MistyWest/polarTracker/Electrical/PCB Output Files/Gerber/PNG export/WW02 Mini RevB Top Silkscreen.pdf

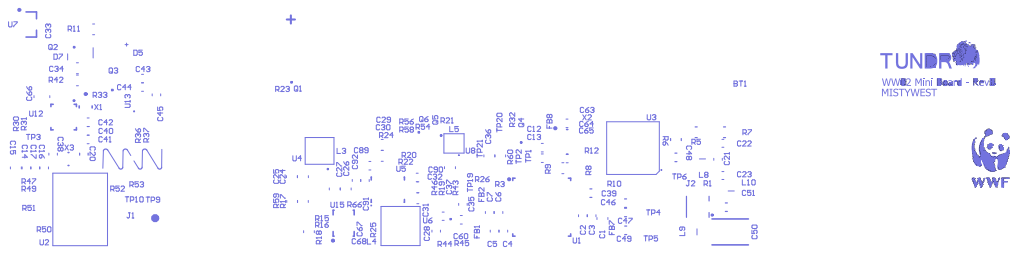
[picture p5: page 1]
