MistyWest/polarTracker/assets/WW02 Bear Tag_Arctic_backup.108.png

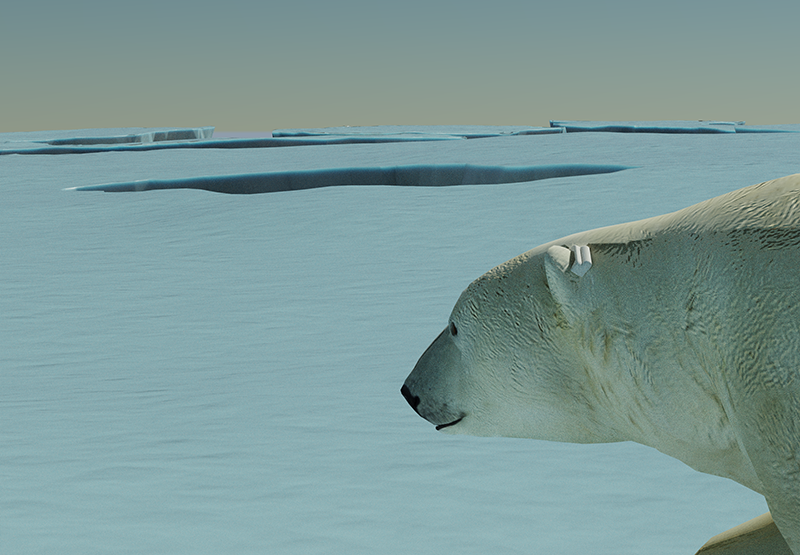
assets/WW02 Bear Tag_Arctic_backup.108.png
