MistyWest/polarTracker/Development Photos/Electrical Photos/image0.jpeg

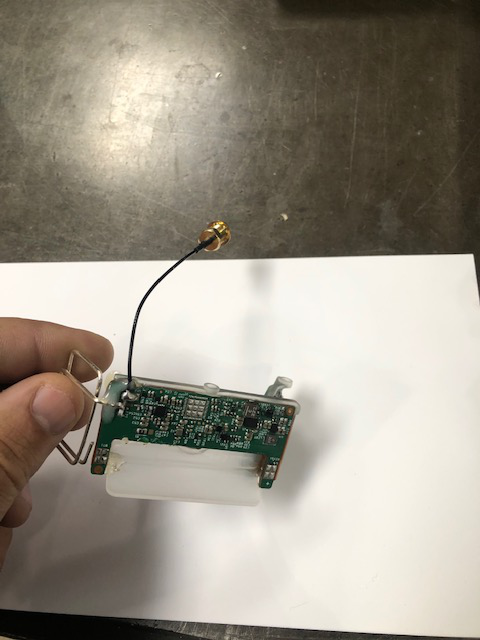
Development Photos/Electrical Photos/image0.jpeg
