MistyWest/polarTracker/Development Photos/Electrical Photos/image1.jpeg

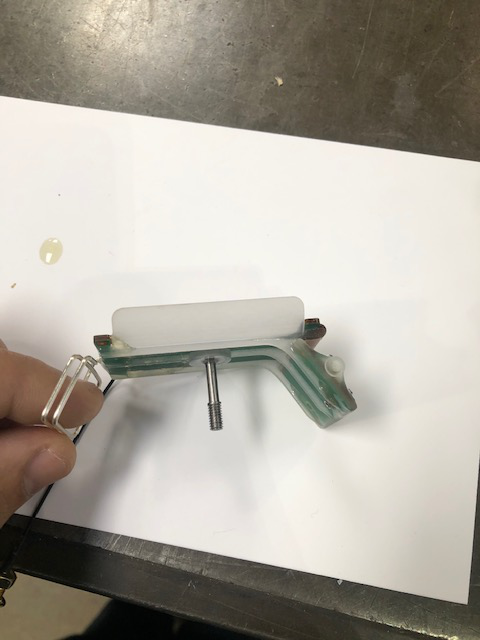
Development Photos/Electrical Photos/image1.jpeg
