MistyWest/polarTracker/Development Photos/Electrical Photos/image2.jpeg

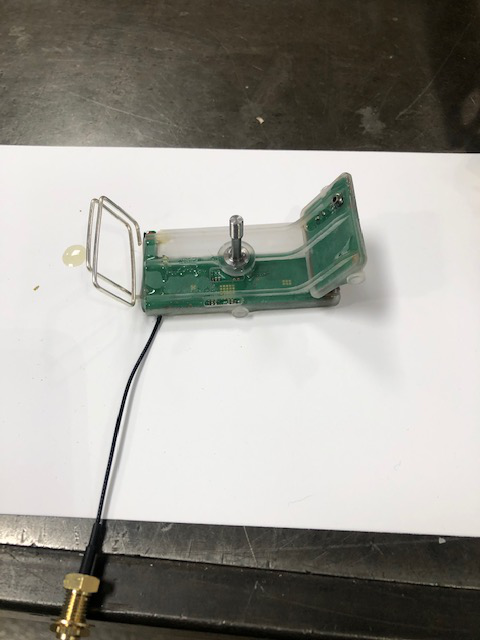
Development Photos/Electrical Photos/image2.jpeg
