MistyWest/polarTracker/Development Photos/Electrical Photos/PCB on Mount, U.FL Connector.jpg

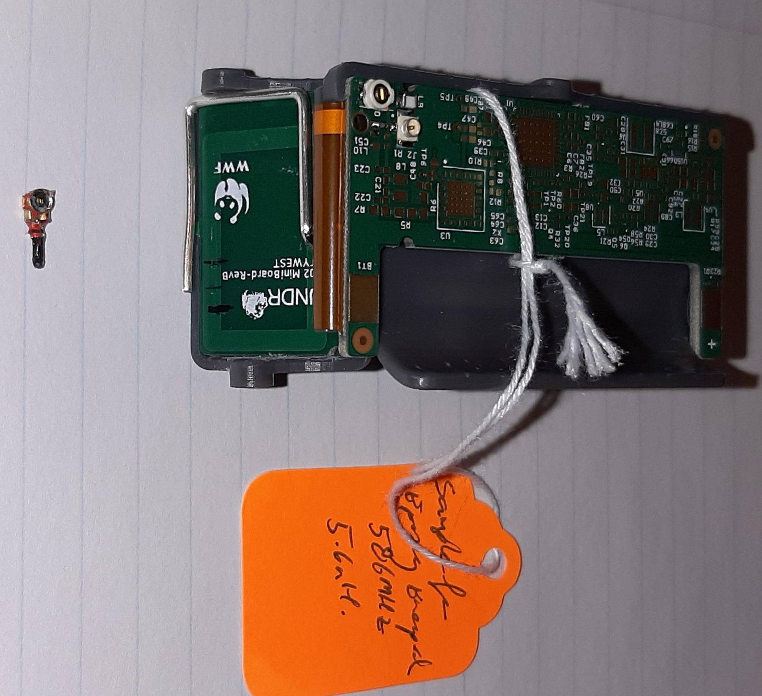
Development Photos/Electrical Photos/PCB on Mount, U.FL Connector.jpg
