MistyWest/polarTracker/Development Photos/Electrical Photos/PCB on Mount, UFL in place.jpg

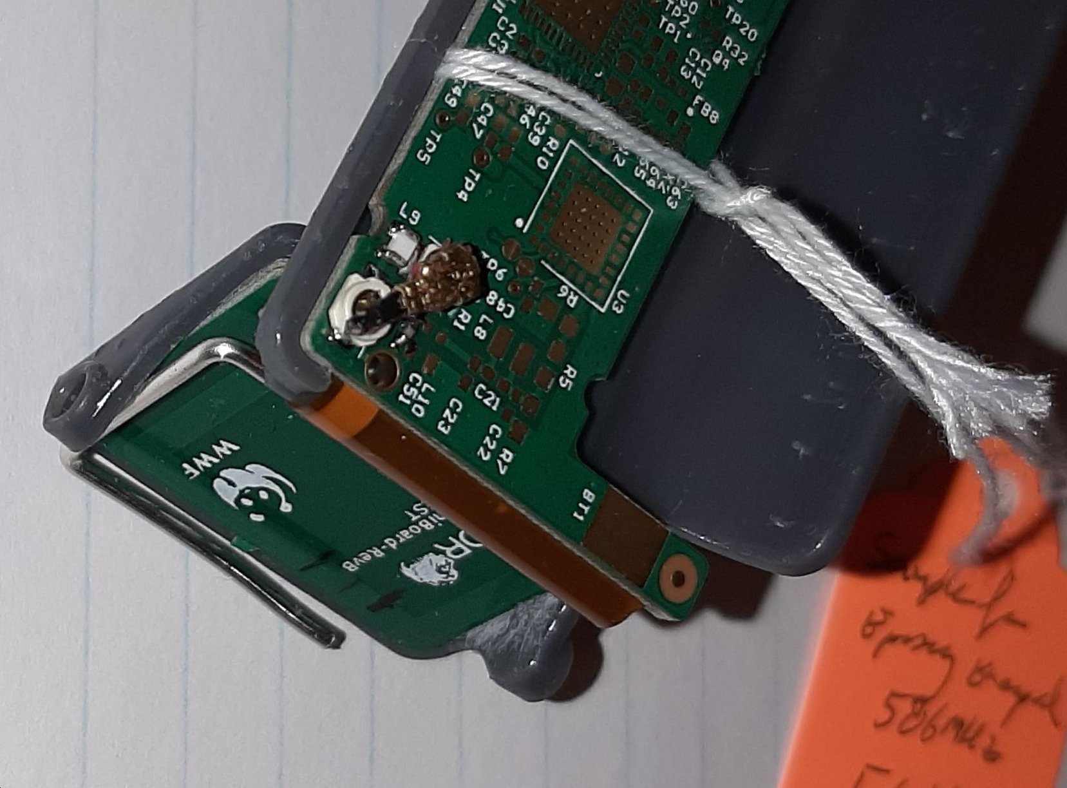
Development Photos/Electrical Photos/PCB on Mount, UFL in place.jpg
