MistyWest/polarTracker/Development Photos/Screenshot 2022-05-12 171735.png

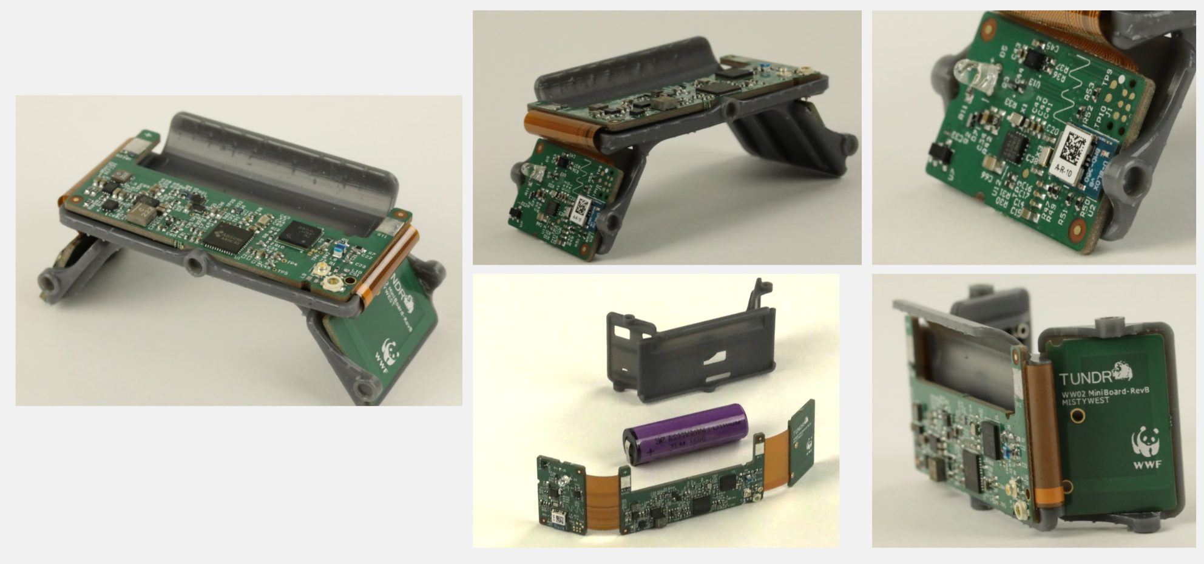
Development Photos/Screenshot 2022-05-12 171735.png
