MistyWest/polarTracker/Development Photos/Screenshot 2022-05-12 171948.png

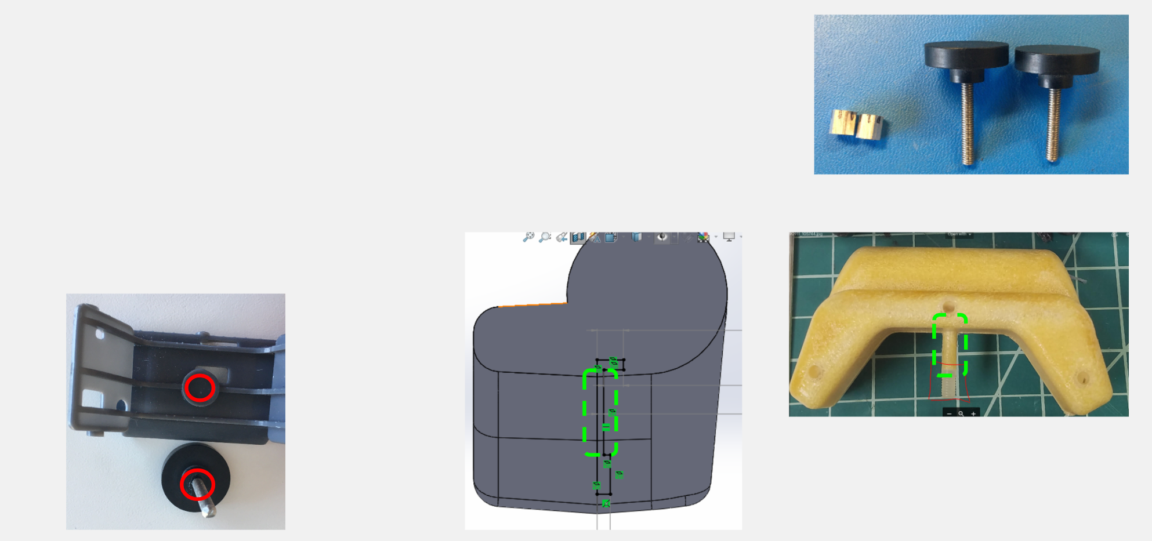
Development Photos/Screenshot 2022-05-12 171948.png
