MistyWest/polarTracker/Development Photos/Screenshot 2022-05-12 172118.png

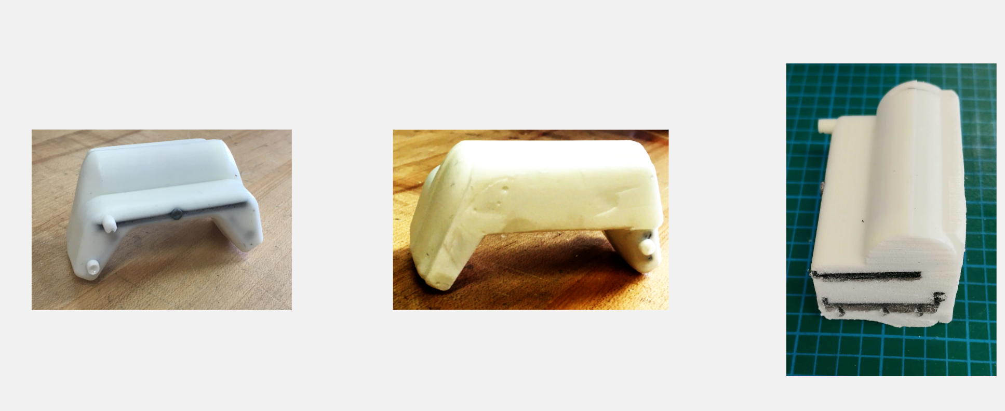
Development Photos/Screenshot 2022-05-12 172118.png
