MistyWest/polarTracker/Development Photos/Screenshot 2022-05-12 172450.png

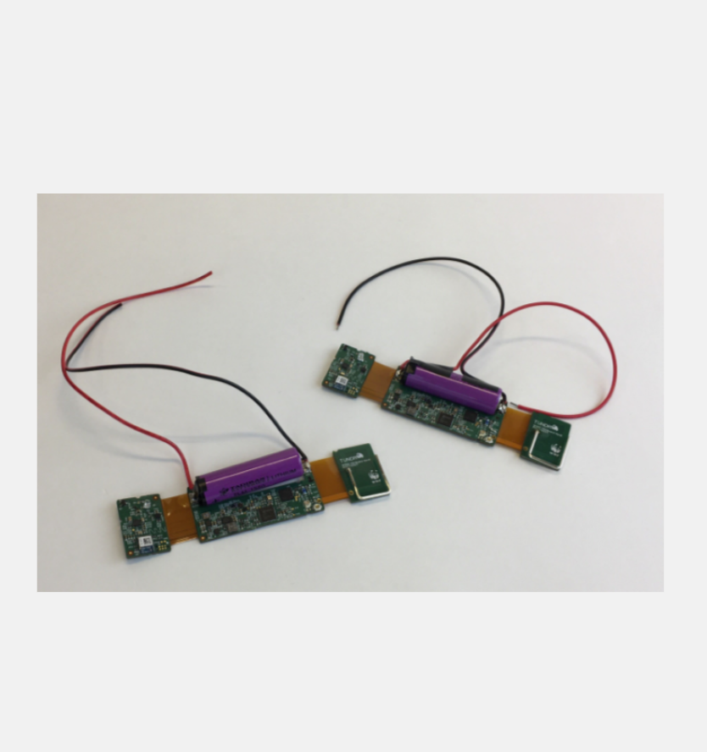
Development Photos/Screenshot 2022-05-12 172450.png
