MistyWest/polarTracker/Development Photos/Screenshot 2022-05-12 172559.png

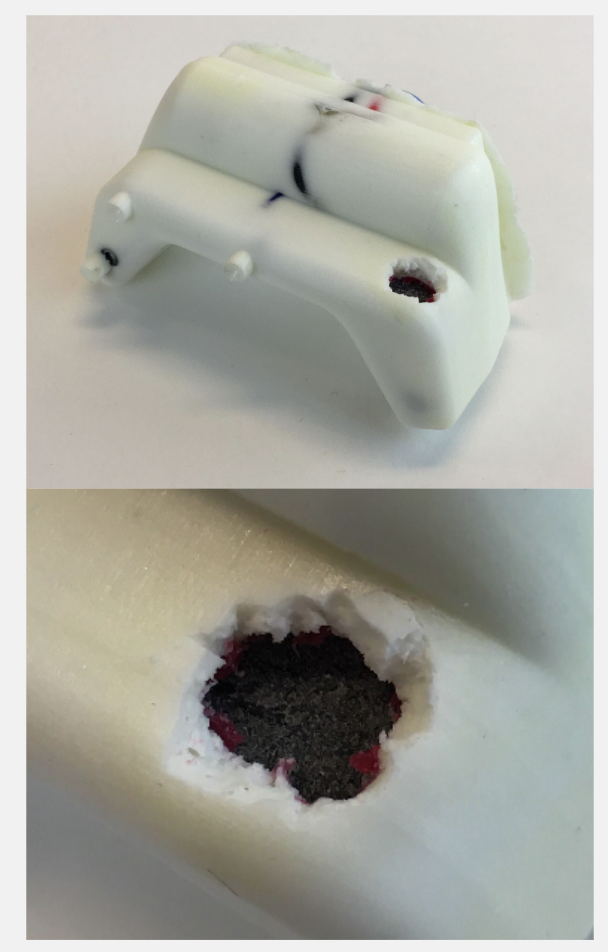
Development Photos/Screenshot 2022-05-12 172559.png
