MistyWest/polarTracker/Development Photos/Screenshot 2022-05-12 173209.png

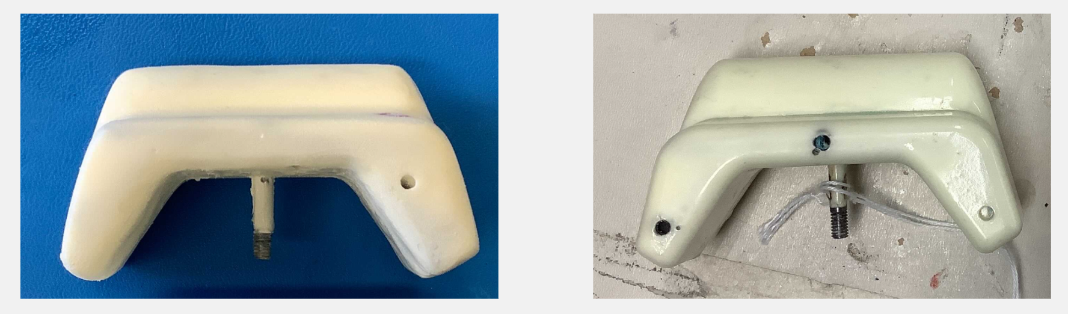
Development Photos/Screenshot 2022-05-12 173209.png
