MistyWest/polarTracker/Development Photos/Screenshot 2022-05-12 173252.png

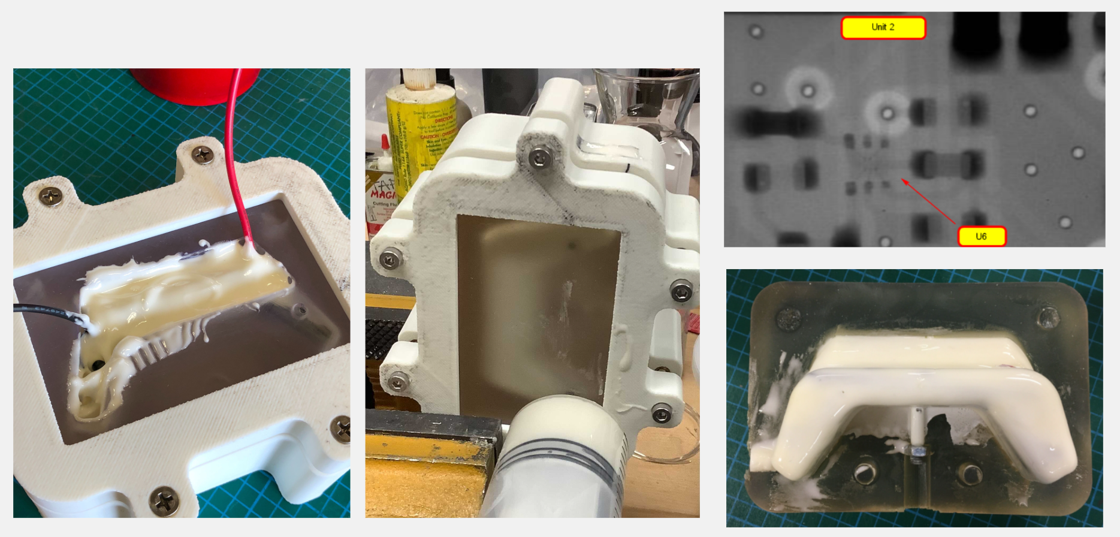
Development Photos/Screenshot 2022-05-12 173252.png
