MistyWest/polarTracker/Development Photos/WWF_340x460.png

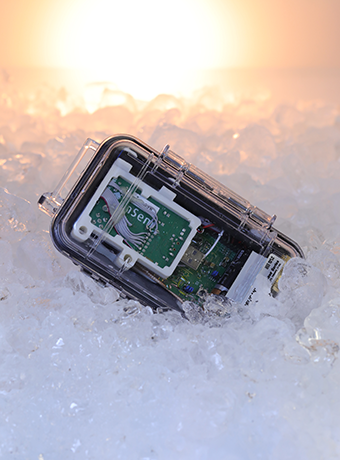
Development Photos/WWF_340x460.png
