MistyWest/polarTracker/Development Photos/WWF_Tracker03.png

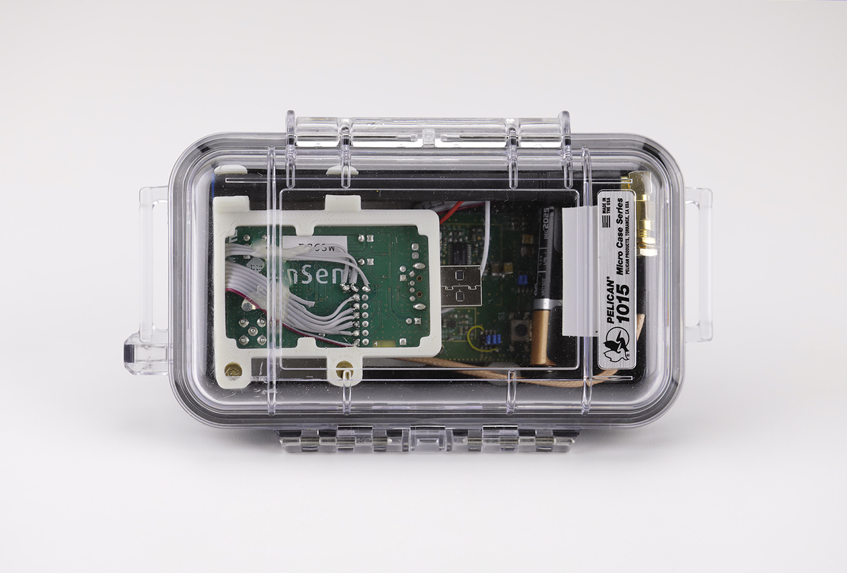
Development Photos/WWF_Tracker03.png
