MistyWest/polarTracker/Electrical/Images/WW02 Mini RevB Top Layer.png

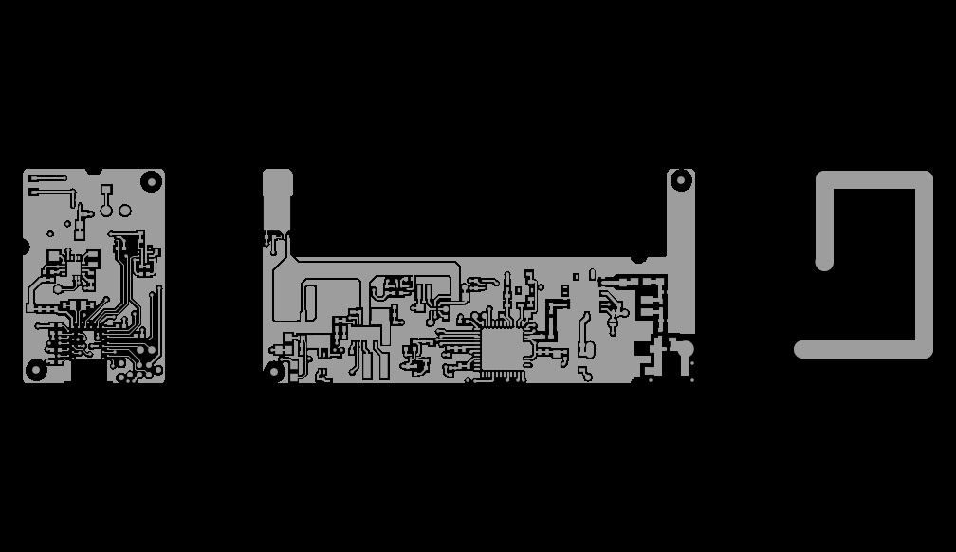
Electrical/Images/WW02 Mini RevB Top Layer.png
