MistyWest/polarTracker/Electrical/Images/WW02 Top Silkscreen.png

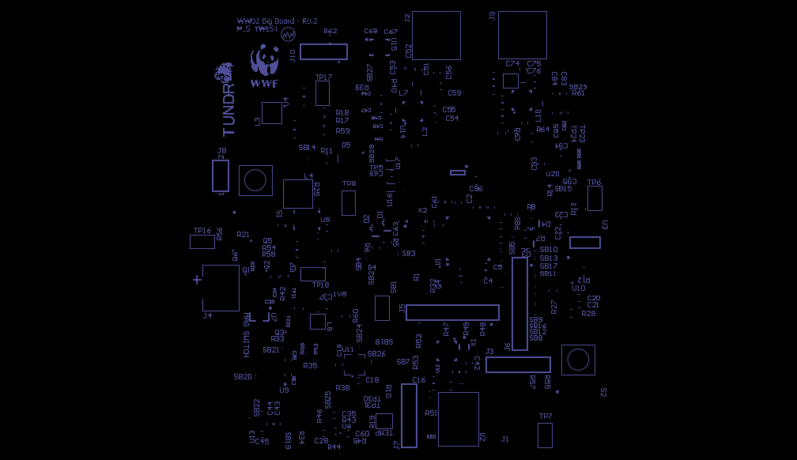
Electrical/Images/WW02 Top Silkscreen.png
