MistyWest/polarTracker/Electrical/Images/WW02_0000s_0003_Top-Layer-Right.png

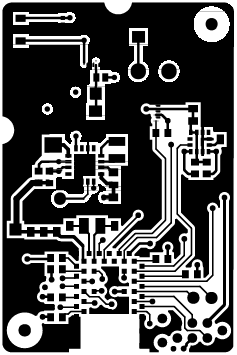
Electrical/Images/WW02_0000s_0003_Top-Layer-Right.png
