MistyWest/polarTracker/Electrical/Images/WW02_0002s_0002_Top-Layer-Middle.png

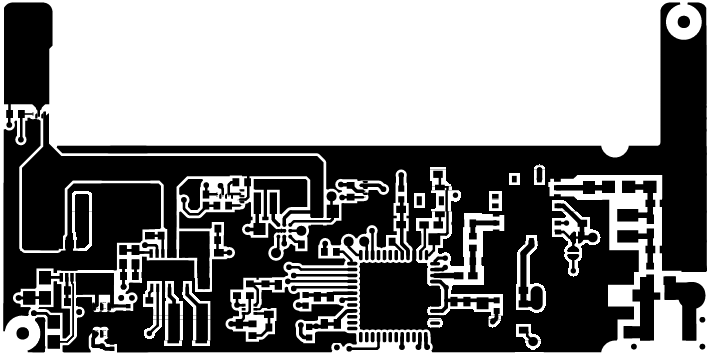
Electrical/Images/WW02_0002s_0002_Top-Layer-Middle.png
