MistyWest/polarTracker/Electrical/PCB Output Files/Gerber/PNG export/Photoshop png export/WW02_0001s_0002_Top-Layer-Antenna.png

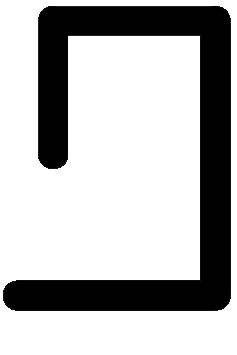
Electrical/PCB Output Files/Gerber/PNG export/Photoshop png export/WW02_0001s_0002_Top-Layer-Antenna.png
