MistyWest/polarTracker/Electrical/PCB Output Files/Gerber/PNG export/Photoshop png export/WW02_0002s_0000_Silkscreen-Middle.png

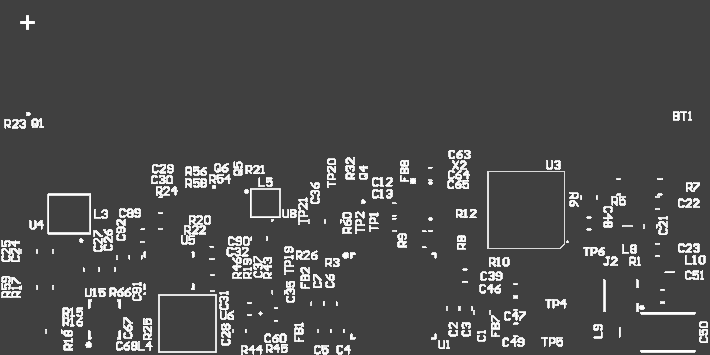
Electrical/PCB Output Files/Gerber/PNG export/Photoshop png export/WW02_0002s_0000_Silkscreen-Middle.png
