MistyWest/polarTracker/Electrical/PCB Output Files/Gerber/PNG export/Photoshop png export/WW02_0003s_0002_Top-Layer-copy-3.png

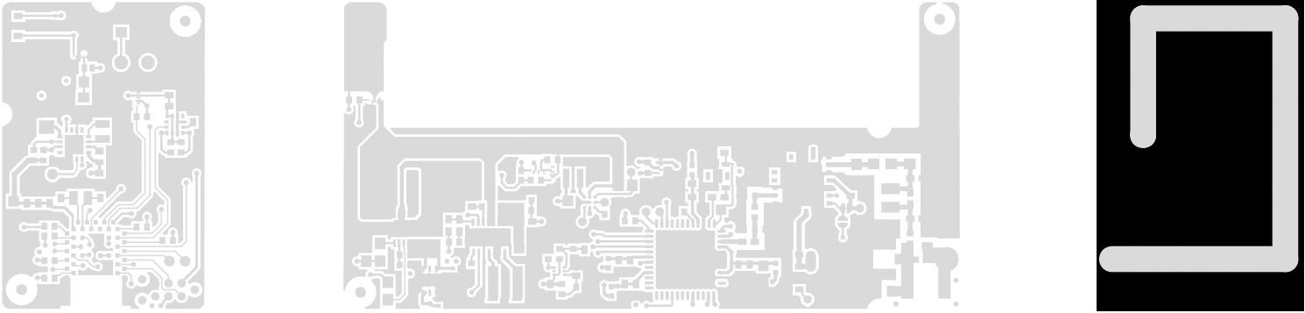
Electrical/PCB Output Files/Gerber/PNG export/Photoshop png export/WW02_0003s_0002_Top-Layer-copy-3.png
