MistyWest/polarTracker/Electrical/PCB Output Files/Gerber/PNG export/Photoshop png export/WW02_0003s_0003_Outline.png

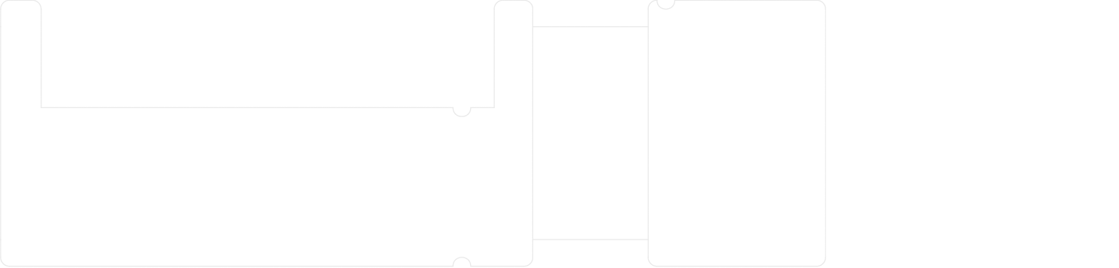
Electrical/PCB Output Files/Gerber/PNG export/Photoshop png export/WW02_0003s_0003_Outline.png
