MistyWest/polarTracker/Electrical/PCB Output Files/Gerber/PNG export/Silkscreen Antenna.png

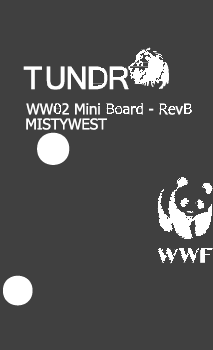
Electrical/PCB Output Files/Gerber/PNG export/Silkscreen Antenna.png
