MistyWest/polarTracker/Electrical/PCB Output Files/Gerber/PNG export/Silkscreen Right.png

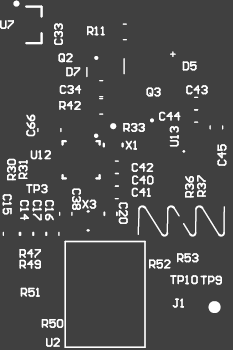
Electrical/PCB Output Files/Gerber/PNG export/Silkscreen Right.png
