MistyWest/polarTracker/Electrical/PCB Output Files/Gerber/PNG export/WW02 Mini RevB Board Outline.png

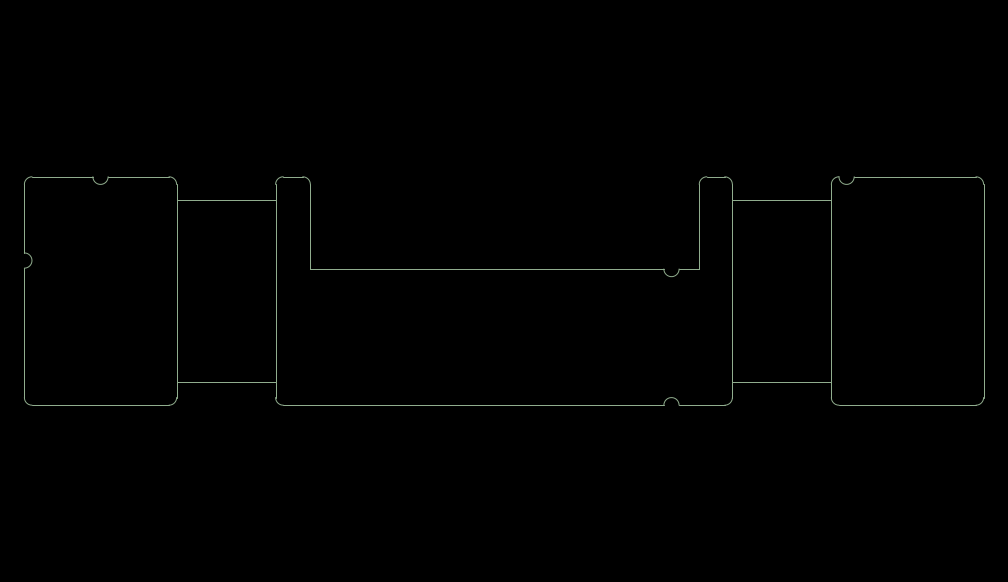
Electrical/PCB Output Files/Gerber/PNG export/WW02 Mini RevB Board Outline.png
