MistyWest/polarTracker/Electrical/PCB Output Files/Gerber/PNG export/WW02 Outline.png

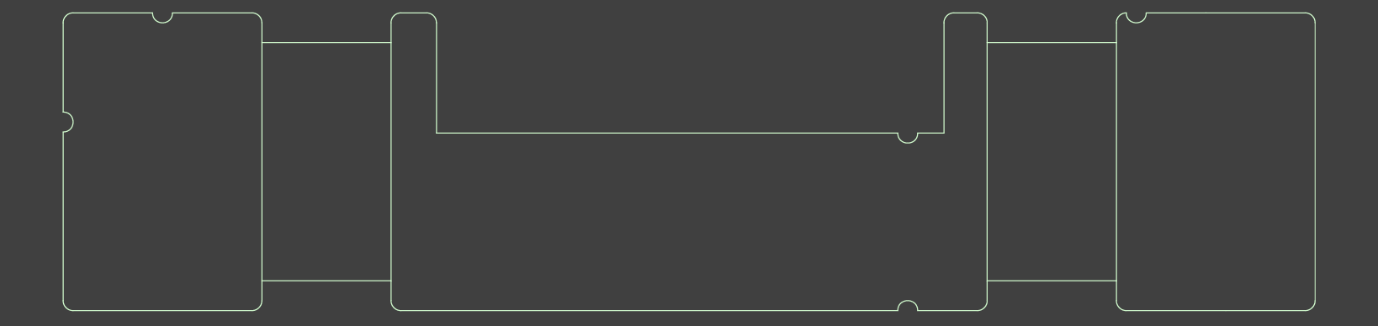
Electrical/PCB Output Files/Gerber/PNG export/WW02 Outline.png
