MistyWest/polarTracker/Electrical/PCB Output Files/Gerber/PNG export/WW02 Top Layer.png

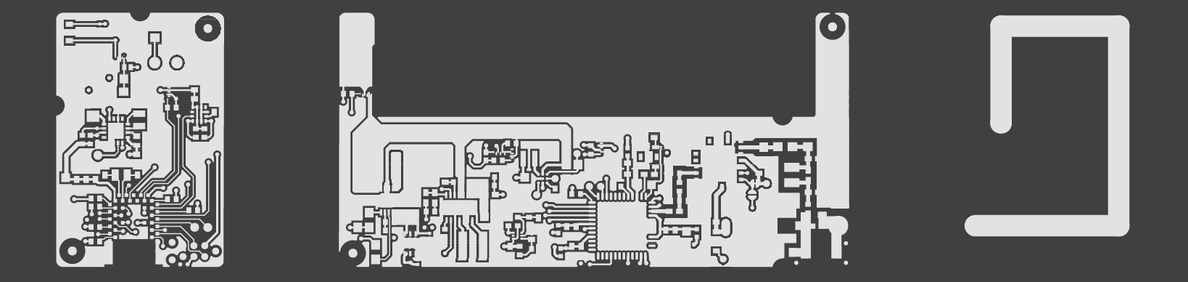
Electrical/PCB Output Files/Gerber/PNG export/WW02 Top Layer.png
