MistyWest/polarTracker/Electrical/PCB Output Files/Gerber/PNG export/WW02 Top Silkscreen.png

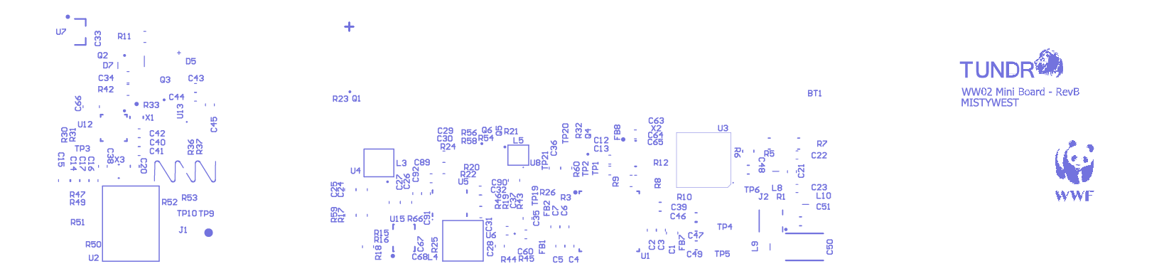
Electrical/PCB Output Files/Gerber/PNG export/WW02 Top Silkscreen.png
