MistyWest/polarTracker/Electrical/PCB Output Files/Gerber/PNG export/WW02_0000s_0001_Silkscreen-Right.png

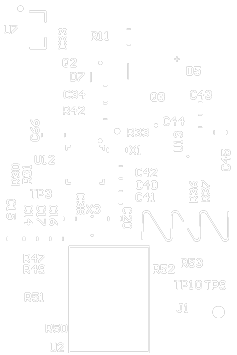
Electrical/PCB Output Files/Gerber/PNG export/WW02_0000s_0001_Silkscreen-Right.png
