MistyWest/polarTracker/Electrical/PCB Output Files/Gerber/PNG export/WW02_0001s_0000_Silkscreen-Antenna.png

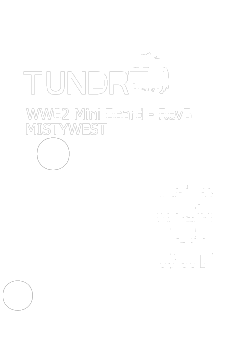
Electrical/PCB Output Files/Gerber/PNG export/WW02_0001s_0000_Silkscreen-Antenna.png
