MistyWest/polarTracker/Electrical/PCB Output Files/Stackup.jpg

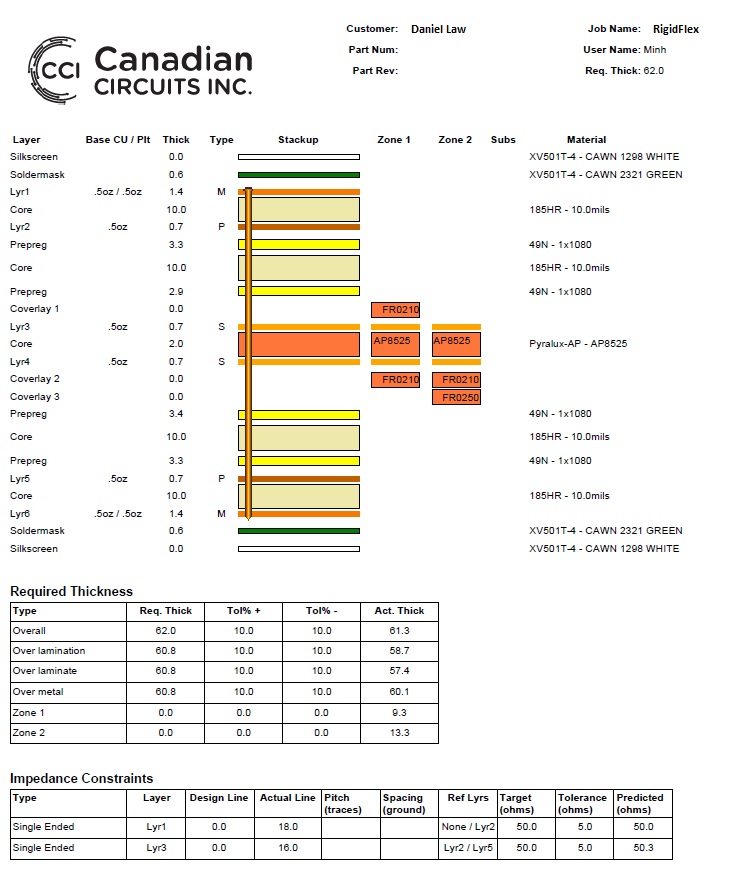
Electrical/PCB Output Files/Stackup.jpg
