MistyWest/polarTracker/Mechanical/3D Printed Mold v3/Hardware/90591A109_Zinc-Plated Steel Hex Nut.SLDPRT

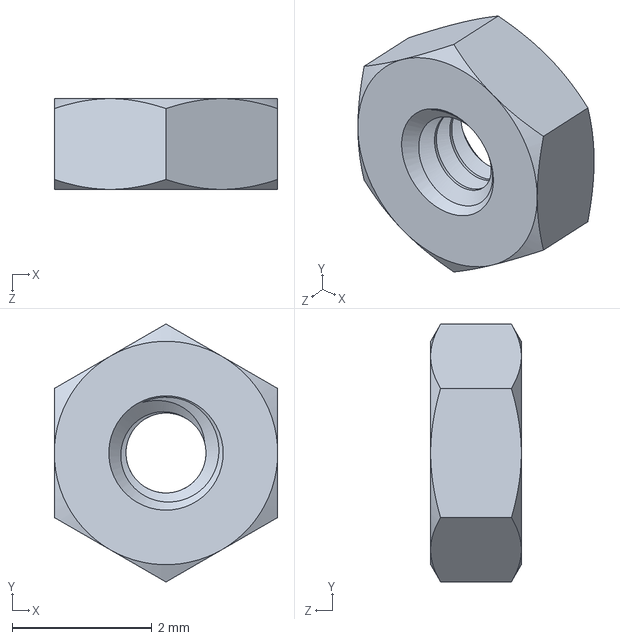
[picture p64: CAD file, 2022-04-27]
Mechanical/3D Printed Mold v3/Hardware/90591A109_Zinc-Plated Steel Hex Nut.SLDPRT
3.20 x 3.70 x 1.30 mm
