MistyWest/polarTracker/Mechanical/Mold v3/Hardware/90592A090_STEEL HEX NUT.SLDPRT

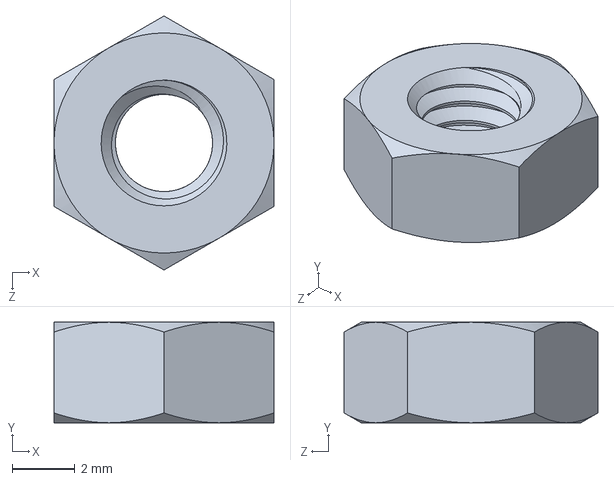
[picture p65: CAD file, 2022-04-28]
Mechanical/Mold v3/Hardware/90592A090_STEEL HEX NUT.SLDPRT
7.00 x 3.20 x 8.08 mm
