MistyWest/polarTracker/Mechanical/3D Printed Mold v3/Hardware/90358A009_Ultra-Low-Profile Socket Head Screw.SLDPRT

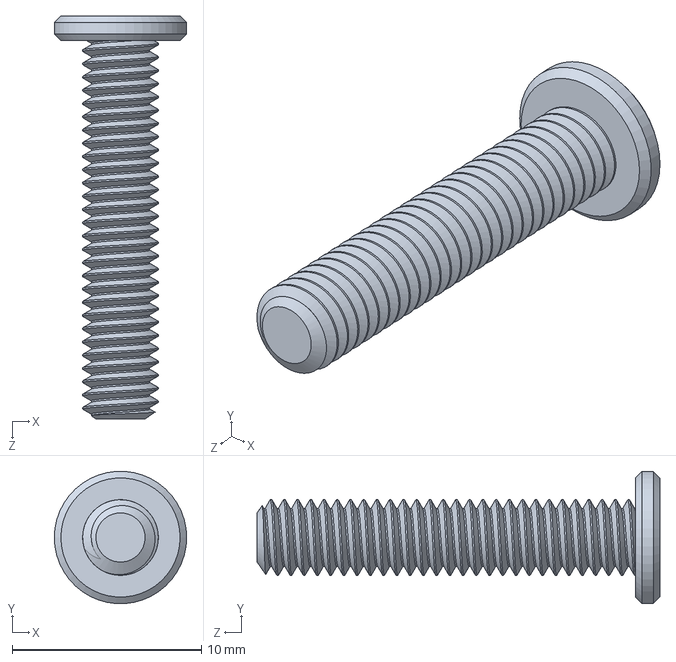
[picture p66: CAD file, 2022-04-27]
Mechanical/3D Printed Mold v3/Hardware/90358A009_Ultra-Low-Profile Socket Head Screw.SLDPRT
7.00 x 6.98 x 21.3 mm
