MistyWest/polarTracker/Mechanical/3D Printed Mold v3/Hardware/M4x0.7mmx20mm Ulow_prof.SLDPRT

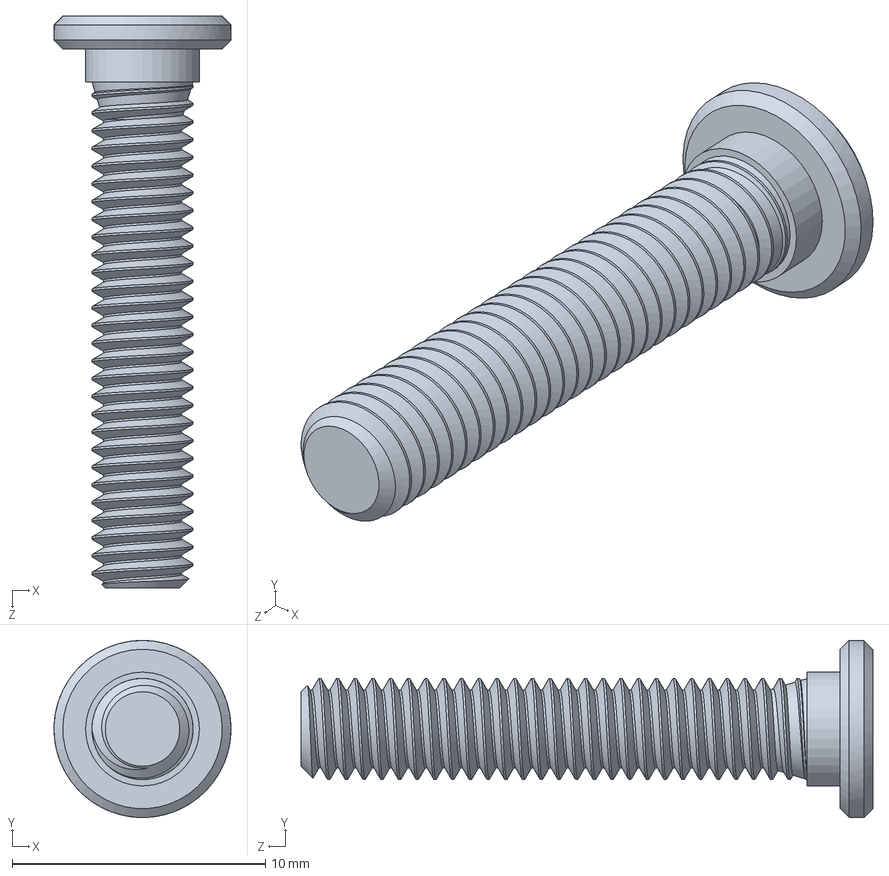
[picture p67: CAD file, 2022-04-27]
Mechanical/3D Printed Mold v3/Hardware/M4x0.7mmx20mm Ulow_prof.SLDPRT
7.00 x 7.00 x 22.6 mm
