MistyWest/polarTracker/Electrical/PCB Output Files/Gerber/PNG export/Photoshop png export/WW02_0000s_0002_Solder-Pads-Right.png

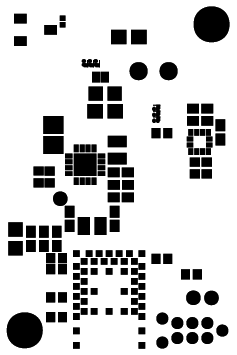
Electrical/PCB Output Files/Gerber/PNG export/Photoshop png export/WW02_0000s_0002_Solder-Pads-Right.png
