MistyWest/polarTracker/Electrical/PCB Output Files/Gerber/PNG export/Photoshop png export/WW02_0002s_0001_Solder-Pads-Middle.png

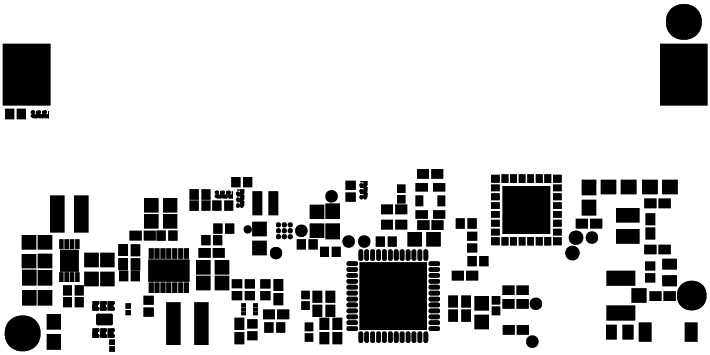
Electrical/PCB Output Files/Gerber/PNG export/Photoshop png export/WW02_0002s_0001_Solder-Pads-Middle.png
