MistyWest/polarTracker/Electrical/PCB Output Files/Gerber/PNG export/Solder Pads Right.png

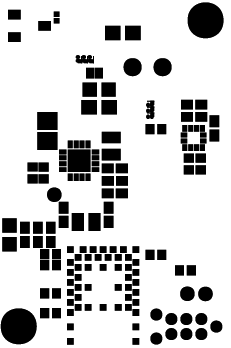
Electrical/PCB Output Files/Gerber/PNG export/Solder Pads Right.png
