MistyWest/polarTracker/Electrical/PCB Output Files/Gerber/PNG export/WW02 Mini RevB Solder Pads.png

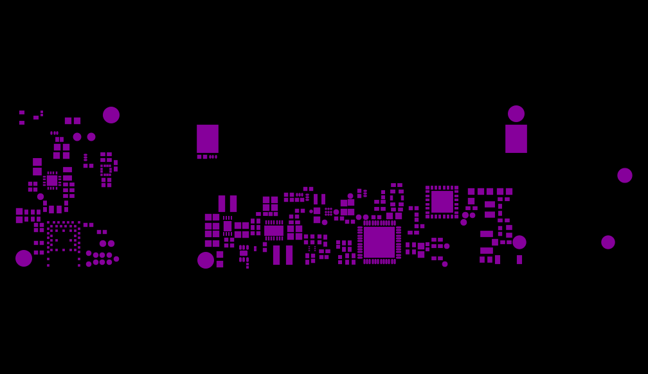
Electrical/PCB Output Files/Gerber/PNG export/WW02 Mini RevB Solder Pads.png
