MistyWest/polarTracker/Electrical/PCB Output Files/Gerber/PNG export/WW02 Solder.png

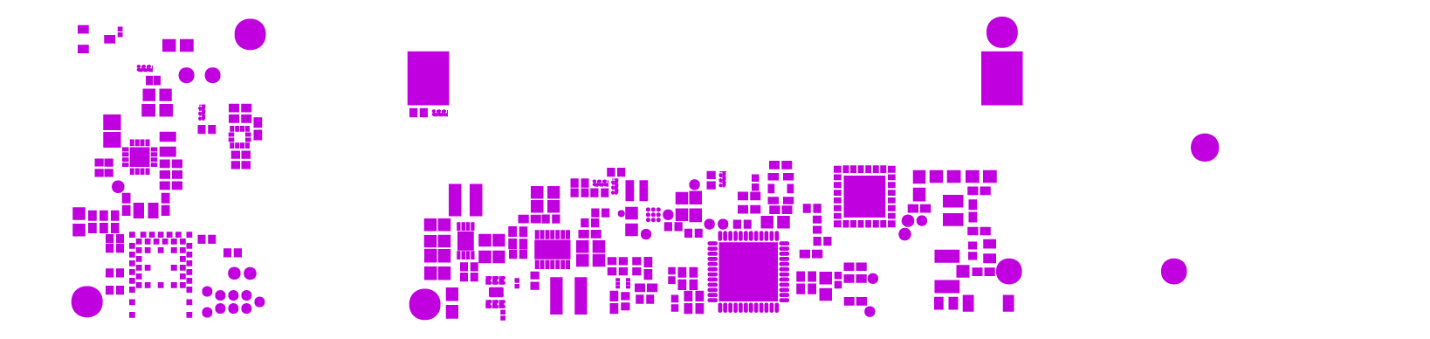
Electrical/PCB Output Files/Gerber/PNG export/WW02 Solder.png
