MistyWest/polarTracker/Testing and RF/Antenna versions, mounted tests.jpg

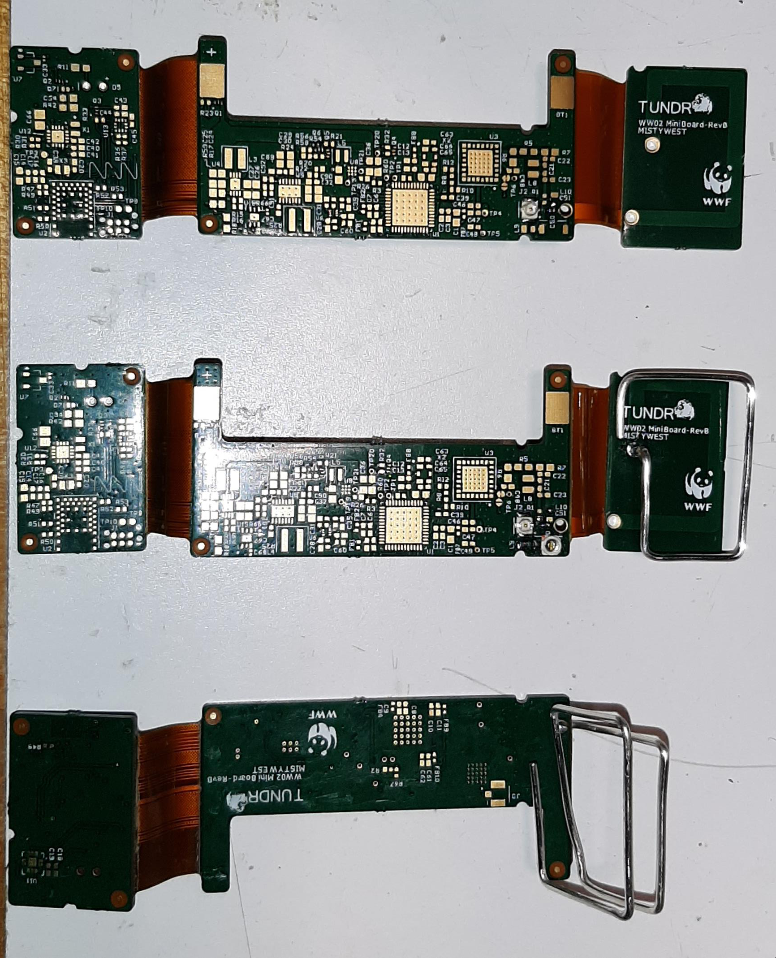
Testing and RF/Antenna versions, mounted tests.jpg
