MistyWest/polarTracker/Testing and RF/Hybrid Antenna on Test Unit.jpg

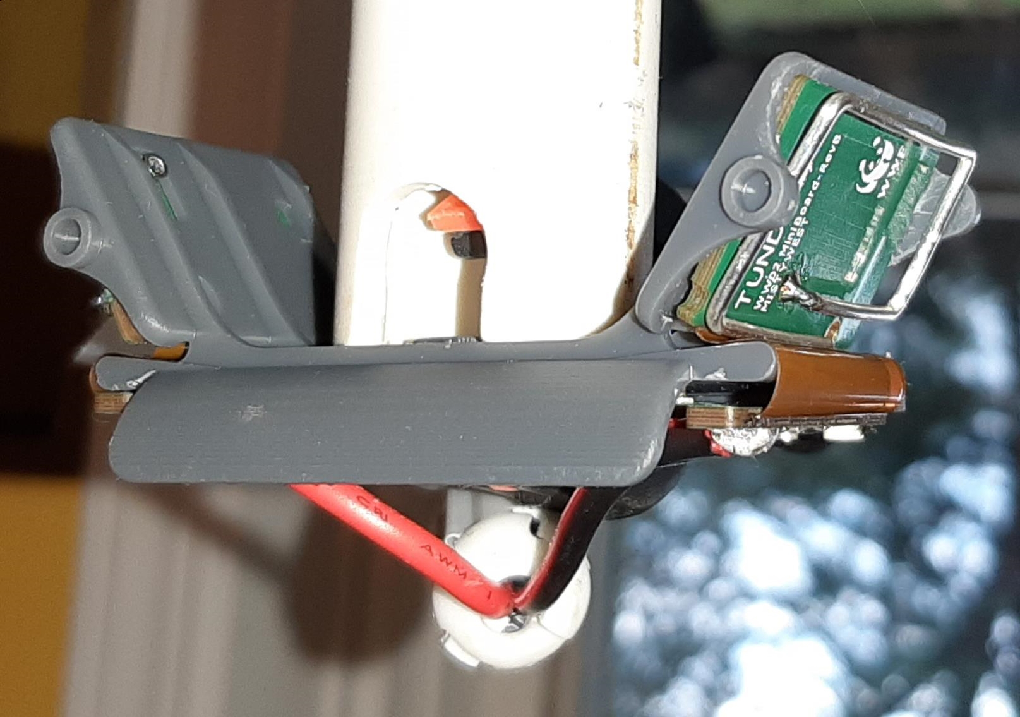
Testing and RF/Hybrid Antenna on Test Unit.jpg
