MistyWest/polarTracker/Testing and RF/IDEO_Feb_20.jpg

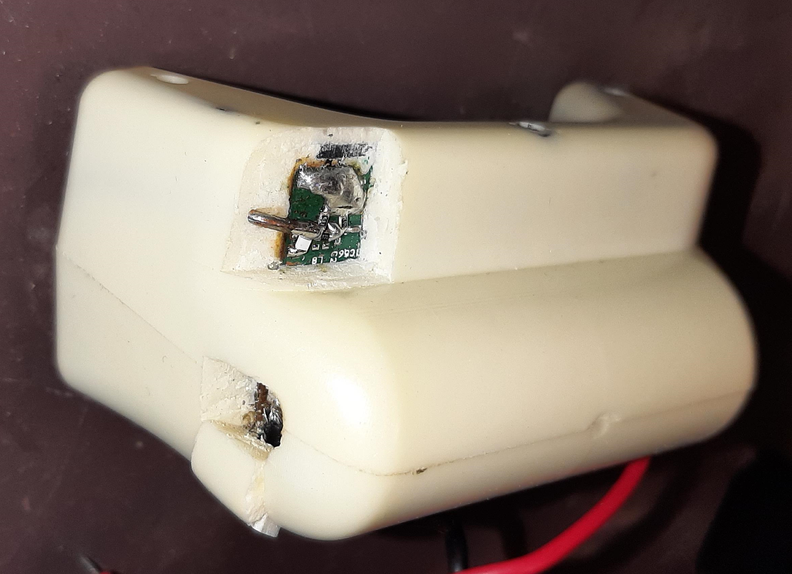
Testing and RF/IDEO_Feb_20.jpg
