MistyWest/polarTracker/Testing and RF/MW_Mar_21.jpg

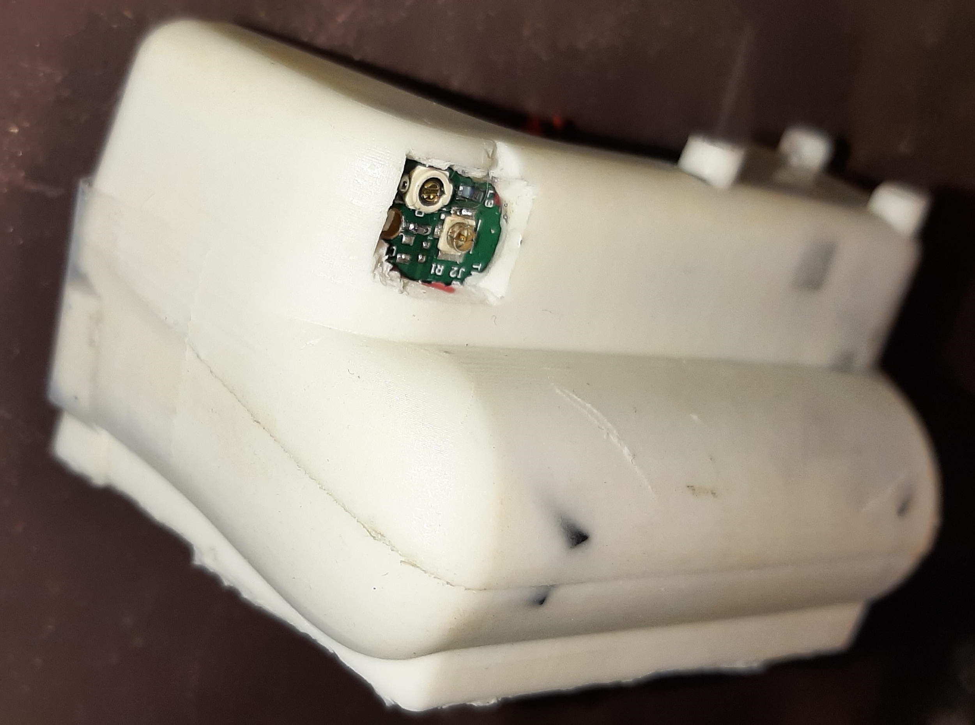
Testing and RF/MW_Mar_21.jpg
