MistyWest/polarTracker/Electrical/PCB Output Files/Gerber/PNG export/WW02 Mini RevB Top Layer.pdf

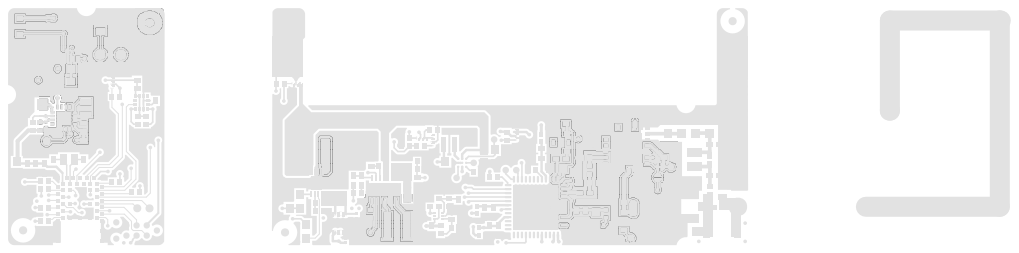
[picture p127: page 1]
