MistyWest/polarTracker/Firmware/ww02Firmware/CLI_Logging/mw_cli_settings.h

/*
 * mw_cli_settings.h
 *
 *  Created on: Jul 23, 2019
 *      Author: klockwood
 */

#ifndef CLI_LOGGING_MW_CLI_SETTINGS_H_
#define CLI_LOGGING_MW_CLI_SETTINGS_H_

#define CLI_TAG                                 "MistyWest>>"

#define cmdMAX_INPUT_SIZE                       100
#define cmdMAX_OUTPUT_SIZE                      100
#define cmdSOCKET_INPUT_BUFFER_SIZE             100

#define TIME_OUT                                20000

#define CLI_BUFFER_SIZE                         512
#define TX_BUF_SIZE                             2048
#define RX_BUF_SIZE                             256


#define CLI_THREAD_LOOP_DELAY                   200

#endif /* CLI_LOGGING_MW_CLI_SETTINGS_H_ */
