MistyWest/polarTracker/Firmware/ww02Firmware/SPI/mw_spi_device_settings.h

/*
 * spi_device_settings.h
 *
 *  Created on: Jan 21, 2019
 *      Author: klockwood
 */

/**@file
 *
 * @defgroup mw_spi_settings SPI Settings
 * @{
 * @ingroup  mw_spi
 * @brief    SPI settings.
 */

#ifndef SPI_MW_SPI_DEVICE_SETTINGS_H_
#define SPI_MW_SPI_DEVICE_SETTINGS_H_

#include "nrf_spi.h"
#include "nrf_spim.h"
#include "nrfx_spim.h"


#endif /* SPI_MW_SPI_DEVICE_SETTINGS_H_ */
