MistyWest/polarTracker/Firmware/ww02Firmware/mw_watchdog.h

/*
 * mw_watchdog.h
 *
 *  Created on: Oct 13, 2020
 *      Author: klockwood
 */

#ifndef UTIL_MW_WATCHDOG_H_
#define UTIL_MW_WATCHDOG_H_



void mw_watchdog_enable();

/**
 * @brief - Initializes WatchDog - Autostarts
 */
void mw_watchdog_init();

#endif /* UTIL_MW_WATCHDOG_H_ */
