MistyWest/polarTracker/Firmware/wwf_bootloader/_project_custom_board/config/sdk_config.h

/**
 * Copyright (c) 2017 - 2018, Nordic Semiconductor ASA
 *
 * All rights reserved.
 *
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
 * 3. Neither the name of Nordic Semiconductor ASA nor the names of its
 *    contributors may be used to endorse or promote products derived from this
 *    software without specific prior written permission.
 *
 * 4. This software, with or without modification, must only be used with a
 *    Nordic Semiconductor ASA integrated circuit.
 *
 * 5. Any software provided in binary form under this license must not be reverse
 *    engineered, decompiled, modified and/or disassembled.
 *
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
 */



#ifndef SDK_CONFIG_H
#define SDK_CONFIG_H
// <<< Use Configuration Wizard in Context Menu >>>\n

/* Use Project defined settings */
#include "mw_ble_dfu_settings.h"

#ifdef USE_APP_CONFIG
#include "app_config.h"
#endif
// <h> nRF_Bootloader

//==========================================================
// <h> nrf_bootloader - Bootloader settings

//==========================================================
// <h> Application integrity checks

//==========================================================
// <q> NRF_BL_APP_CRC_CHECK_SKIPPED_ON_GPREGRET2  - Skip integrity check of the application when bit 1 (0-indexed) is set in the GPREGRET2 register.


#ifndef NRF_BL_APP_CRC_CHECK_SKIPPED_ON_GPREGRET2
#define NRF_BL_APP_CRC_CHECK_SKIPPED_ON_GPREGRET2 1
#endif

// <q> NRF_BL_APP_CRC_CHECK_SKIPPED_ON_SYSTEMOFF_RESET  - Skip integrity check of the application when waking up from the System Off state.


#ifndef NRF_BL_APP_CRC_CHECK_SKIPPED_ON_SYSTEMOFF_RESET
#define NRF_BL_APP_CRC_CHECK_SKIPPED_ON_SYSTEMOFF_RESET 1
#endif

// </h>
//==========================================================

// <h> DFU mode enter method

//==========================================================
// <e> NRF_BL_DFU_ENTER_METHOD_BUTTON - Enter DFU mode on button press.
//==========================================================
#ifndef NRF_BL_DFU_ENTER_METHOD_BUTTON
#define NRF_BL_DFU_ENTER_METHOD_BUTTON 0
#endif
// <o> NRF_BL_DFU_ENTER_METHOD_BUTTON_PIN  - Button for entering DFU mode.

// <0=> 0 (P0.0)
// <1=> 1 (P0.1)
// <2=> 2 (P0.2)
// <3=> 3 (P0.3)
// <4=> 4 (P0.4)
// <5=> 5 (P0.5)
// <6=> 6 (P0.6)
// <7=> 7 (P0.7)
// <8=> 8 (P0.8)
// <9=> 9 (P0.9)
// <10=> 10 (P0.10)
// <11=> 11 (P0.11)
// <12=> 12 (P0.12)
// <13=> 13 (P0.13)
// <14=> 14 (P0.14)
// <15=> 15 (P0.15)
// <16=> 16 (P0.16)
// <17=> 17 (P0.17)
// <18=> 18 (P0.18)
// <19=> 19 (P0.19)
// <20=> 20 (P0.20)
// <21=> 21 (P0.21)
// <22=> 22 (P0.22)
// <23=> 23 (P0.23)
// <24=> 24 (P0.24)
// <25=> 25 (P0.25)
// <26=> 26 (P0.26)
// <27=> 27 (P0.27)
// <28=> 28 (P0.28)
// <29=> 29 (P0.29)
// <30=> 30 (P0.30)
// <31=> 31 (P0.31)

#ifndef NRF_BL_DFU_ENTER_METHOD_BUTTON_PIN
#define NRF_BL_DFU_ENTER_METHOD_BUTTON_PIN 16
#endif

// </e>

// <q> NRF_BL_DFU_ENTER_METHOD_PINRESET  - Enter DFU mode on pin reset.


#ifndef NRF_BL_DFU_ENTER_METHOD_PINRESET
#define NRF_BL_DFU_ENTER_METHOD_PINRESET 0
#endif

// <q> NRF_BL_DFU_ENTER_METHOD_GPREGRET  - Enter DFU mode when bit 1 (0-indexed) is set in the NRF_POWER_GPREGRET register.


#ifndef NRF_BL_DFU_ENTER_METHOD_GPREGRET
#define NRF_BL_DFU_ENTER_METHOD_GPREGRET 1
#endif

// <q> NRF_BL_DFU_ENTER_METHOD_BUTTONLESS  - Enter DFU mode when the Boolean enter_buttonless_dfu in DFU settings is true.


#ifndef NRF_BL_DFU_ENTER_METHOD_BUTTONLESS
#define NRF_BL_DFU_ENTER_METHOD_BUTTONLESS 0
#endif

// </h>
//==========================================================

// <h> DFU timers

//==========================================================
// <o> NRF_BL_DFU_CONTINUATION_TIMEOUT_MS - Timeout in ms when expecting an update immediately.  <100-60000000>


// <i> This timeout is used after updating the SoftDevice, when there is
// <i> already a valid application present. The bootloader will enter DFU mode
// <i> for a short time instead of booting the old application to allow the host
// <i> to immediately transfer a new application if it wishes.

#ifndef NRF_BL_DFU_CONTINUATION_TIMEOUT_MS
#define NRF_BL_DFU_CONTINUATION_TIMEOUT_MS 10000
#endif

// <o> NRF_BL_DFU_INACTIVITY_TIMEOUT_MS - Timeout in ms before automatically starting a valid application due to inactivity.  <0-60000000>


// <i> If 0, no inactivity timer will be used. Values 1-99 are invalid.

#ifndef NRF_BL_DFU_INACTIVITY_TIMEOUT_MS
#define NRF_BL_DFU_INACTIVITY_TIMEOUT_MS 120000
#endif

// </h>
//==========================================================

// <h> Watchdog timer

//==========================================================
// <o> NRF_BL_WDT_MAX_SCHEDULER_LATENCY_MS - Maximum latency of the scheduler in miliseconds
// <i> Maximum latency of the scheduler is compared with
// <i> watchdog counter reload value (CRV). If latency is big
// <i> enough, the watchdog will be fed from internal timer
// <i> handler along with feed from user function. If latency
// <i> is smaller than CRV, the watchdog will not be internally fed once
// <i> it will be externally fed. Maximum latency is mainly affected
// <i> by flash operations.

#ifndef NRF_BL_WDT_MAX_SCHEDULER_LATENCY_MS
#define NRF_BL_WDT_MAX_SCHEDULER_LATENCY_MS 10000
#endif

// </h>
//==========================================================

// <h> Misc Bootloader settings

//==========================================================
// <o> NRF_BL_FW_COPY_PROGRESS_STORE_STEP - Number of pages copied after which progress in the settings page is updated.
// <i> Progress stored in the settings page allows the bootloader to resume
// <i> copying the new firmware in case of interruption (reset).
// <i> If the value is small, then the resume point is more accurate. However,
// <i>  it also impacts negatively on flash wear.

#ifndef NRF_BL_FW_COPY_PROGRESS_STORE_STEP
#define NRF_BL_FW_COPY_PROGRESS_STORE_STEP 8
#endif

// </h>
//==========================================================

// </h>
//==========================================================

// </h>
//==========================================================

// <h> nRF_Crypto

//==========================================================
// <e> NRF_CRYPTO_ENABLED - nrf_crypto - Cryptography library.
//==========================================================
#ifndef NRF_CRYPTO_ENABLED
#define NRF_CRYPTO_ENABLED 1
#endif
// <o> NRF_CRYPTO_ALLOCATOR  - Memory allocator


// <i> Choose memory allocator used by nrf_crypto. Default is alloca if possible or nrf_malloc otherwise. If 'User macros' are selected, the user has to create 'nrf_crypto_allocator.h' file that contains NRF_CRYPTO_ALLOC, NRF_CRYPTO_FREE, and NRF_CRYPTO_ALLOC_ON_STACK.
// <0=> Default
// <1=> User macros
// <2=> On stack (alloca)
// <3=> C dynamic memory (malloc)
// <4=> SDK Memory Manager (nrf_malloc)

#ifndef NRF_CRYPTO_ALLOCATOR
#define NRF_CRYPTO_ALLOCATOR 0
#endif

// <e> NRF_CRYPTO_BACKEND_CC310_BL_ENABLED - Enable the ARM Cryptocell CC310 reduced backend.

// <i> The CC310 hardware-accelerated cryptography backend with reduced functionality and footprint (only available on nRF52840).
//==========================================================
#ifndef NRF_CRYPTO_BACKEND_CC310_BL_ENABLED
#define NRF_CRYPTO_BACKEND_CC310_BL_ENABLED 0
#endif
// <q> NRF_CRYPTO_BACKEND_CC310_BL_ECC_SECP224R1_ENABLED  - Enable the secp224r1 elliptic curve support using CC310_BL.


#ifndef NRF_CRYPTO_BACKEND_CC310_BL_ECC_SECP224R1_ENABLED
#define NRF_CRYPTO_BACKEND_CC310_BL_ECC_SECP224R1_ENABLED 0
#endif

// <q> NRF_CRYPTO_BACKEND_CC310_BL_ECC_SECP256R1_ENABLED  - Enable the secp256r1 elliptic curve support using CC310_BL.


#ifndef NRF_CRYPTO_BACKEND_CC310_BL_ECC_SECP256R1_ENABLED
#define NRF_CRYPTO_BACKEND_CC310_BL_ECC_SECP256R1_ENABLED 1
#endif

// <q> NRF_CRYPTO_BACKEND_CC310_BL_HASH_SHA256_ENABLED  - CC310_BL SHA-256 hash functionality.


// <i> CC310_BL backend implementation for hardware-accelerated SHA-256.

#ifndef NRF_CRYPTO_BACKEND_CC310_BL_HASH_SHA256_ENABLED
#define NRF_CRYPTO_BACKEND_CC310_BL_HASH_SHA256_ENABLED 1
#endif

// <q> NRF_CRYPTO_BACKEND_CC310_BL_HASH_AUTOMATIC_RAM_BUFFER_ENABLED  - nrf_cc310_bl buffers to RAM before running hash operation


// <i> Enabling this makes hashing of addresses in FLASH range possible. Size of buffer allocated for hashing is set by NRF_CRYPTO_BACKEND_CC310_BL_HASH_AUTOMATIC_RAM_BUFFER_SIZE

#ifndef NRF_CRYPTO_BACKEND_CC310_BL_HASH_AUTOMATIC_RAM_BUFFER_ENABLED
#define NRF_CRYPTO_BACKEND_CC310_BL_HASH_AUTOMATIC_RAM_BUFFER_ENABLED 0
#endif

// <o> NRF_CRYPTO_BACKEND_CC310_BL_HASH_AUTOMATIC_RAM_BUFFER_SIZE - nrf_cc310_bl hash outputs digests in little endian
// <i> Makes the nrf_cc310_bl hash functions output digests in little endian format. Only for use in nRF SDK DFU!

#ifndef NRF_CRYPTO_BACKEND_CC310_BL_HASH_AUTOMATIC_RAM_BUFFER_SIZE
#define NRF_CRYPTO_BACKEND_CC310_BL_HASH_AUTOMATIC_RAM_BUFFER_SIZE 4096
#endif

// </e>

// <e> NRF_CRYPTO_BACKEND_CC310_ENABLED - Enable the ARM Cryptocell CC310 backend.

// <i> The CC310 hardware-accelerated cryptography backend (only available on nRF52840).
//==========================================================
#ifndef NRF_CRYPTO_BACKEND_CC310_ENABLED
#define NRF_CRYPTO_BACKEND_CC310_ENABLED 0
#endif
// <q> NRF_CRYPTO_BACKEND_CC310_AES_CBC_ENABLED  - Enable the AES CBC mode using CC310.


#ifndef NRF_CRYPTO_BACKEND_CC310_AES_CBC_ENABLED
#define NRF_CRYPTO_BACKEND_CC310_AES_CBC_ENABLED 1
#endif

// <q> NRF_CRYPTO_BACKEND_CC310_AES_CTR_ENABLED  - Enable the AES CTR mode using CC310.


#ifndef NRF_CRYPTO_BACKEND_CC310_AES_CTR_ENABLED
#define NRF_CRYPTO_BACKEND_CC310_AES_CTR_ENABLED 1
#endif

// <q> NRF_CRYPTO_BACKEND_CC310_AES_ECB_ENABLED  - Enable the AES ECB mode using CC310.


#ifndef NRF_CRYPTO_BACKEND_CC310_AES_ECB_ENABLED
#define NRF_CRYPTO_BACKEND_CC310_AES_ECB_ENABLED 1
#endif

// <q> NRF_CRYPTO_BACKEND_CC310_AES_CBC_MAC_ENABLED  - Enable the AES CBC_MAC mode using CC310.


#ifndef NRF_CRYPTO_BACKEND_CC310_AES_CBC_MAC_ENABLED
#define NRF_CRYPTO_BACKEND_CC310_AES_CBC_MAC_ENABLED 1
#endif

// <q> NRF_CRYPTO_BACKEND_CC310_AES_CMAC_ENABLED  - Enable the AES CMAC mode using CC310.


#ifndef NRF_CRYPTO_BACKEND_CC310_AES_CMAC_ENABLED
#define NRF_CRYPTO_BACKEND_CC310_AES_CMAC_ENABLED 1
#endif

// <q> NRF_CRYPTO_BACKEND_CC310_AES_CCM_ENABLED  - Enable the AES CCM mode using CC310.


#ifndef NRF_CRYPTO_BACKEND_CC310_AES_CCM_ENABLED
#define NRF_CRYPTO_BACKEND_CC310_AES_CCM_ENABLED 1
#endif

// <q> NRF_CRYPTO_BACKEND_CC310_AES_CCM_STAR_ENABLED  - Enable the AES CCM* mode using CC310.


#ifndef NRF_CRYPTO_BACKEND_CC310_AES_CCM_STAR_ENABLED
#define NRF_CRYPTO_BACKEND_CC310_AES_CCM_STAR_ENABLED 1
#endif

// <q> NRF_CRYPTO_BACKEND_CC310_CHACHA_POLY_ENABLED  - Enable the CHACHA-POLY mode using CC310.


#ifndef NRF_CRYPTO_BACKEND_CC310_CHACHA_POLY_ENABLED
#define NRF_CRYPTO_BACKEND_CC310_CHACHA_POLY_ENABLED 1
#endif

// <q> NRF_CRYPTO_BACKEND_CC310_ECC_SECP160R1_ENABLED  - Enable the secp160r1 elliptic curve support using CC310.


#ifndef NRF_CRYPTO_BACKEND_CC310_ECC_SECP160R1_ENABLED
#define NRF_CRYPTO_BACKEND_CC310_ECC_SECP160R1_ENABLED 1
#endif

// <q> NRF_CRYPTO_BACKEND_CC310_ECC_SECP160R2_ENABLED  - Enable the secp160r2 elliptic curve support using CC310.


#ifndef NRF_CRYPTO_BACKEND_CC310_ECC_SECP160R2_ENABLED
#define NRF_CRYPTO_BACKEND_CC310_ECC_SECP160R2_ENABLED 1
#endif

// <q> NRF_CRYPTO_BACKEND_CC310_ECC_SECP192R1_ENABLED  - Enable the secp192r1 elliptic curve support using CC310.


#ifndef NRF_CRYPTO_BACKEND_CC310_ECC_SECP192R1_ENABLED
#define NRF_CRYPTO_BACKEND_CC310_ECC_SECP192R1_ENABLED 1
#endif

// <q> NRF_CRYPTO_BACKEND_CC310_ECC_SECP224R1_ENABLED  - Enable the secp224r1 elliptic curve support using CC310.


#ifndef NRF_CRYPTO_BACKEND_CC310_ECC_SECP224R1_ENABLED
#define NRF_CRYPTO_BACKEND_CC310_ECC_SECP224R1_ENABLED 1
#endif

// <q> NRF_CRYPTO_BACKEND_CC310_ECC_SECP256R1_ENABLED  - Enable the secp256r1 elliptic curve support using CC310.


#ifndef NRF_CRYPTO_BACKEND_CC310_ECC_SECP256R1_ENABLED
#define NRF_CRYPTO_BACKEND_CC310_ECC_SECP256R1_ENABLED 1
#endif

// <q> NRF_CRYPTO_BACKEND_CC310_ECC_SECP384R1_ENABLED  - Enable the secp384r1 elliptic curve support using CC310.


#ifndef NRF_CRYPTO_BACKEND_CC310_ECC_SECP384R1_ENABLED
#define NRF_CRYPTO_BACKEND_CC310_ECC_SECP384R1_ENABLED 1
#endif

// <q> NRF_CRYPTO_BACKEND_CC310_ECC_SECP521R1_ENABLED  - Enable the secp521r1 elliptic curve support using CC310.


#ifndef NRF_CRYPTO_BACKEND_CC310_ECC_SECP521R1_ENABLED
#define NRF_CRYPTO_BACKEND_CC310_ECC_SECP521R1_ENABLED 1
#endif

// <q> NRF_CRYPTO_BACKEND_CC310_ECC_SECP160K1_ENABLED  - Enable the secp160k1 elliptic curve support using CC310.


#ifndef NRF_CRYPTO_BACKEND_CC310_ECC_SECP160K1_ENABLED
#define NRF_CRYPTO_BACKEND_CC310_ECC_SECP160K1_ENABLED 1
#endif

// <q> NRF_CRYPTO_BACKEND_CC310_ECC_SECP192K1_ENABLED  - Enable the secp192k1 elliptic curve support using CC310.


#ifndef NRF_CRYPTO_BACKEND_CC310_ECC_SECP192K1_ENABLED
#define NRF_CRYPTO_BACKEND_CC310_ECC_SECP192K1_ENABLED 1
#endif

// <q> NRF_CRYPTO_BACKEND_CC310_ECC_SECP224K1_ENABLED  - Enable the secp224k1 elliptic curve support using CC310.


#ifndef NRF_CRYPTO_BACKEND_CC310_ECC_SECP224K1_ENABLED
#define NRF_CRYPTO_BACKEND_CC310_ECC_SECP224K1_ENABLED 1
#endif

// <q> NRF_CRYPTO_BACKEND_CC310_ECC_SECP256K1_ENABLED  - Enable the secp256k1 elliptic curve support using CC310.


#ifndef NRF_CRYPTO_BACKEND_CC310_ECC_SECP256K1_ENABLED
#define NRF_CRYPTO_BACKEND_CC310_ECC_SECP256K1_ENABLED 1
#endif

// <q> NRF_CRYPTO_BACKEND_CC310_ECC_CURVE25519_ENABLED  - Enable the Curve25519 curve support using CC310.


#ifndef NRF_CRYPTO_BACKEND_CC310_ECC_CURVE25519_ENABLED
#define NRF_CRYPTO_BACKEND_CC310_ECC_CURVE25519_ENABLED 1
#endif

// <q> NRF_CRYPTO_BACKEND_CC310_ECC_ED25519_ENABLED  - Enable the Ed25519 curve support using CC310.


#ifndef NRF_CRYPTO_BACKEND_CC310_ECC_ED25519_ENABLED
#define NRF_CRYPTO_BACKEND_CC310_ECC_ED25519_ENABLED 1
#endif

// <q> NRF_CRYPTO_BACKEND_CC310_HASH_SHA256_ENABLED  - CC310 SHA-256 hash functionality.


// <i> CC310 backend implementation for hardware-accelerated SHA-256.

#ifndef NRF_CRYPTO_BACKEND_CC310_HASH_SHA256_ENABLED
#define NRF_CRYPTO_BACKEND_CC310_HASH_SHA256_ENABLED 1
#endif

// <q> NRF_CRYPTO_BACKEND_CC310_HASH_SHA512_ENABLED  - CC310 SHA-512 hash functionality


// <i> CC310 backend implementation for SHA-512 (in software).

#ifndef NRF_CRYPTO_BACKEND_CC310_HASH_SHA512_ENABLED
#define NRF_CRYPTO_BACKEND_CC310_HASH_SHA512_ENABLED 1
#endif

// <q> NRF_CRYPTO_BACKEND_CC310_HMAC_SHA256_ENABLED  - CC310 HMAC using SHA-256


// <i> CC310 backend implementation for HMAC using hardware-accelerated SHA-256.

#ifndef NRF_CRYPTO_BACKEND_CC310_HMAC_SHA256_ENABLED
#define NRF_CRYPTO_BACKEND_CC310_HMAC_SHA256_ENABLED 1
#endif

// <q> NRF_CRYPTO_BACKEND_CC310_HMAC_SHA512_ENABLED  - CC310 HMAC using SHA-512


// <i> CC310 backend implementation for HMAC using SHA-512 (in software).

#ifndef NRF_CRYPTO_BACKEND_CC310_HMAC_SHA512_ENABLED
#define NRF_CRYPTO_BACKEND_CC310_HMAC_SHA512_ENABLED 1
#endif

// <q> NRF_CRYPTO_BACKEND_CC310_RNG_ENABLED  - Enable RNG support using CC310.


#ifndef NRF_CRYPTO_BACKEND_CC310_RNG_ENABLED
#define NRF_CRYPTO_BACKEND_CC310_RNG_ENABLED 1
#endif

// </e>

// <e> NRF_CRYPTO_BACKEND_CIFRA_ENABLED - Enable the Cifra backend.
//==========================================================
#ifndef NRF_CRYPTO_BACKEND_CIFRA_ENABLED
#define NRF_CRYPTO_BACKEND_CIFRA_ENABLED 0
#endif
// <q> NRF_CRYPTO_BACKEND_CIFRA_AES_EAX_ENABLED  - Enable the AES EAX mode using Cifra.


#ifndef NRF_CRYPTO_BACKEND_CIFRA_AES_EAX_ENABLED
#define NRF_CRYPTO_BACKEND_CIFRA_AES_EAX_ENABLED 1
#endif

// </e>

// <e> NRF_CRYPTO_BACKEND_MBEDTLS_ENABLED - Enable the mbed TLS backend.
//==========================================================
#ifndef NRF_CRYPTO_BACKEND_MBEDTLS_ENABLED
#define NRF_CRYPTO_BACKEND_MBEDTLS_ENABLED 0
#endif
// <q> NRF_CRYPTO_BACKEND_MBEDTLS_AES_CBC_ENABLED  - Enable the AES CBC mode mbed TLS.


#ifndef NRF_CRYPTO_BACKEND_MBEDTLS_AES_CBC_ENABLED
#define NRF_CRYPTO_BACKEND_MBEDTLS_AES_CBC_ENABLED 1
#endif

// <q> NRF_CRYPTO_BACKEND_MBEDTLS_AES_CTR_ENABLED  - Enable the AES CTR mode using mbed TLS.


#ifndef NRF_CRYPTO_BACKEND_MBEDTLS_AES_CTR_ENABLED
#define NRF_CRYPTO_BACKEND_MBEDTLS_AES_CTR_ENABLED 1
#endif

// <q> NRF_CRYPTO_BACKEND_MBEDTLS_AES_CFB_ENABLED  - Enable the AES CFB mode using mbed TLS.


#ifndef NRF_CRYPTO_BACKEND_MBEDTLS_AES_CFB_ENABLED
#define NRF_CRYPTO_BACKEND_MBEDTLS_AES_CFB_ENABLED 1
#endif

// <q> NRF_CRYPTO_BACKEND_MBEDTLS_AES_ECB_ENABLED  - Enable the AES ECB mode using mbed TLS.


#ifndef NRF_CRYPTO_BACKEND_MBEDTLS_AES_ECB_ENABLED
#define NRF_CRYPTO_BACKEND_MBEDTLS_AES_ECB_ENABLED 1
#endif

// <q> NRF_CRYPTO_BACKEND_MBEDTLS_AES_CBC_MAC_ENABLED  - Enable the AES CBC MAC mode using mbed TLS.


#ifndef NRF_CRYPTO_BACKEND_MBEDTLS_AES_CBC_MAC_ENABLED
#define NRF_CRYPTO_BACKEND_MBEDTLS_AES_CBC_MAC_ENABLED 1
#endif

// <q> NRF_CRYPTO_BACKEND_MBEDTLS_AES_CMAC_ENABLED  - Enable the AES CMAC mode using mbed TLS.


#ifndef NRF_CRYPTO_BACKEND_MBEDTLS_AES_CMAC_ENABLED
#define NRF_CRYPTO_BACKEND_MBEDTLS_AES_CMAC_ENABLED 1
#endif

// <q> NRF_CRYPTO_BACKEND_MBEDTLS_AES_CCM_ENABLED  - Enable the AES CCM mode using mbed TLS.


#ifndef NRF_CRYPTO_BACKEND_MBEDTLS_AES_CCM_ENABLED
#define NRF_CRYPTO_BACKEND_MBEDTLS_AES_CCM_ENABLED 1
#endif

// <q> NRF_CRYPTO_BACKEND_MBEDTLS_AES_GCM_ENABLED  - Enable the AES GCM mode using mbed TLS.


#ifndef NRF_CRYPTO_BACKEND_MBEDTLS_AES_GCM_ENABLED
#define NRF_CRYPTO_BACKEND_MBEDTLS_AES_GCM_ENABLED 1
#endif

// <q> NRF_CRYPTO_BACKEND_MBEDTLS_ECC_SECP192R1_ENABLED  - Enable secp192r1 (NIST 192-bit) curve


// <i> Enable this setting if you need secp192r1 (NIST 192-bit) support using MBEDTLS

#ifndef NRF_CRYPTO_BACKEND_MBEDTLS_ECC_SECP192R1_ENABLED
#define NRF_CRYPTO_BACKEND_MBEDTLS_ECC_SECP192R1_ENABLED 1
#endif

// <q> NRF_CRYPTO_BACKEND_MBEDTLS_ECC_SECP224R1_ENABLED  - Enable secp224r1 (NIST 224-bit) curve


// <i> Enable this setting if you need secp224r1 (NIST 224-bit) support using MBEDTLS

#ifndef NRF_CRYPTO_BACKEND_MBEDTLS_ECC_SECP224R1_ENABLED
#define NRF_CRYPTO_BACKEND_MBEDTLS_ECC_SECP224R1_ENABLED 1
#endif

// <q> NRF_CRYPTO_BACKEND_MBEDTLS_ECC_SECP256R1_ENABLED  - Enable secp256r1 (NIST 256-bit) curve


// <i> Enable this setting if you need secp256r1 (NIST 256-bit) support using MBEDTLS

#ifndef NRF_CRYPTO_BACKEND_MBEDTLS_ECC_SECP256R1_ENABLED
#define NRF_CRYPTO_BACKEND_MBEDTLS_ECC_SECP256R1_ENABLED 1
#endif

// <q> NRF_CRYPTO_BACKEND_MBEDTLS_ECC_SECP384R1_ENABLED  - Enable secp384r1 (NIST 384-bit) curve


// <i> Enable this setting if you need secp384r1 (NIST 384-bit) support using MBEDTLS

#ifndef NRF_CRYPTO_BACKEND_MBEDTLS_ECC_SECP384R1_ENABLED
#define NRF_CRYPTO_BACKEND_MBEDTLS_ECC_SECP384R1_ENABLED 1
#endif

// <q> NRF_CRYPTO_BACKEND_MBEDTLS_ECC_SECP521R1_ENABLED  - Enable secp521r1 (NIST 521-bit) curve


// <i> Enable this setting if you need secp521r1 (NIST 521-bit) support using MBEDTLS

#ifndef NRF_CRYPTO_BACKEND_MBEDTLS_ECC_SECP521R1_ENABLED
#define NRF_CRYPTO_BACKEND_MBEDTLS_ECC_SECP521R1_ENABLED 1
#endif

// <q> NRF_CRYPTO_BACKEND_MBEDTLS_ECC_SECP192K1_ENABLED  - Enable secp192k1 (Koblitz 192-bit) curve


// <i> Enable this setting if you need secp192k1 (Koblitz 192-bit) support using MBEDTLS

#ifndef NRF_CRYPTO_BACKEND_MBEDTLS_ECC_SECP192K1_ENABLED
#define NRF_CRYPTO_BACKEND_MBEDTLS_ECC_SECP192K1_ENABLED 1
#endif

// <q> NRF_CRYPTO_BACKEND_MBEDTLS_ECC_SECP224K1_ENABLED  - Enable secp224k1 (Koblitz 224-bit) curve


// <i> Enable this setting if you need secp224k1 (Koblitz 224-bit) support using MBEDTLS

#ifndef NRF_CRYPTO_BACKEND_MBEDTLS_ECC_SECP224K1_ENABLED
#define NRF_CRYPTO_BACKEND_MBEDTLS_ECC_SECP224K1_ENABLED 1
#endif

// <q> NRF_CRYPTO_BACKEND_MBEDTLS_ECC_SECP256K1_ENABLED  - Enable secp256k1 (Koblitz 256-bit) curve


// <i> Enable this setting if you need secp256k1 (Koblitz 256-bit) support using MBEDTLS

#ifndef NRF_CRYPTO_BACKEND_MBEDTLS_ECC_SECP256K1_ENABLED
#define NRF_CRYPTO_BACKEND_MBEDTLS_ECC_SECP256K1_ENABLED 1
#endif

// <q> NRF_CRYPTO_BACKEND_MBEDTLS_ECC_BP256R1_ENABLED  - Enable bp256r1 (Brainpool 256-bit) curve


// <i> Enable this setting if you need bp256r1 (Brainpool 256-bit) support using MBEDTLS

#ifndef NRF_CRYPTO_BACKEND_MBEDTLS_ECC_BP256R1_ENABLED
#define NRF_CRYPTO_BACKEND_MBEDTLS_ECC_BP256R1_ENABLED 1
#endif

// <q> NRF_CRYPTO_BACKEND_MBEDTLS_ECC_BP384R1_ENABLED  - Enable bp384r1 (Brainpool 384-bit) curve


// <i> Enable this setting if you need bp384r1 (Brainpool 384-bit) support using MBEDTLS

#ifndef NRF_CRYPTO_BACKEND_MBEDTLS_ECC_BP384R1_ENABLED
#define NRF_CRYPTO_BACKEND_MBEDTLS_ECC_BP384R1_ENABLED 1
#endif

// <q> NRF_CRYPTO_BACKEND_MBEDTLS_ECC_BP512R1_ENABLED  - Enable bp512r1 (Brainpool 512-bit) curve


// <i> Enable this setting if you need bp512r1 (Brainpool 512-bit) support using MBEDTLS

#ifndef NRF_CRYPTO_BACKEND_MBEDTLS_ECC_BP512R1_ENABLED
#define NRF_CRYPTO_BACKEND_MBEDTLS_ECC_BP512R1_ENABLED 1
#endif

// <q> NRF_CRYPTO_BACKEND_MBEDTLS_ECC_CURVE25519_ENABLED  - Enable Curve25519 curve


// <i> Enable this setting if you need Curve25519 support using MBEDTLS

#ifndef NRF_CRYPTO_BACKEND_MBEDTLS_ECC_CURVE25519_ENABLED
#define NRF_CRYPTO_BACKEND_MBEDTLS_ECC_CURVE25519_ENABLED 1
#endif

// <q> NRF_CRYPTO_BACKEND_MBEDTLS_HASH_SHA256_ENABLED  - Enable mbed TLS SHA-256 hash functionality.


// <i> mbed TLS backend implementation for SHA-256.

#ifndef NRF_CRYPTO_BACKEND_MBEDTLS_HASH_SHA256_ENABLED
#define NRF_CRYPTO_BACKEND_MBEDTLS_HASH_SHA256_ENABLED 1
#endif

// <q> NRF_CRYPTO_BACKEND_MBEDTLS_HASH_SHA512_ENABLED  - Enable mbed TLS SHA-512 hash functionality.


// <i> mbed TLS backend implementation for SHA-512.

#ifndef NRF_CRYPTO_BACKEND_MBEDTLS_HASH_SHA512_ENABLED
#define NRF_CRYPTO_BACKEND_MBEDTLS_HASH_SHA512_ENABLED 1
#endif

// <q> NRF_CRYPTO_BACKEND_MBEDTLS_HMAC_SHA256_ENABLED  - Enable mbed TLS HMAC using SHA-256.


// <i> mbed TLS backend implementation for HMAC using SHA-256.

#ifndef NRF_CRYPTO_BACKEND_MBEDTLS_HMAC_SHA256_ENABLED
#define NRF_CRYPTO_BACKEND_MBEDTLS_HMAC_SHA256_ENABLED 1
#endif

// <q> NRF_CRYPTO_BACKEND_MBEDTLS_HMAC_SHA512_ENABLED  - Enable mbed TLS HMAC using SHA-512.


// <i> mbed TLS backend implementation for HMAC using SHA-512.

#ifndef NRF_CRYPTO_BACKEND_MBEDTLS_HMAC_SHA512_ENABLED
#define NRF_CRYPTO_BACKEND_MBEDTLS_HMAC_SHA512_ENABLED 1
#endif

// </e>

// <e> NRF_CRYPTO_BACKEND_MICRO_ECC_ENABLED - Enable the micro-ecc backend.
//==========================================================
#ifndef NRF_CRYPTO_BACKEND_MICRO_ECC_ENABLED
#define NRF_CRYPTO_BACKEND_MICRO_ECC_ENABLED 1
#endif
// <q> NRF_CRYPTO_BACKEND_MICRO_ECC_ECC_SECP192R1_ENABLED  - Enable secp192r1 (NIST 192-bit) curve


// <i> Enable this setting if you need secp192r1 (NIST 192-bit) support using micro-ecc

#ifndef NRF_CRYPTO_BACKEND_MICRO_ECC_ECC_SECP192R1_ENABLED
#define NRF_CRYPTO_BACKEND_MICRO_ECC_ECC_SECP192R1_ENABLED 0
#endif

// <q> NRF_CRYPTO_BACKEND_MICRO_ECC_ECC_SECP224R1_ENABLED  - Enable secp224r1 (NIST 224-bit) curve


// <i> Enable this setting if you need secp224r1 (NIST 224-bit) support using micro-ecc

#ifndef NRF_CRYPTO_BACKEND_MICRO_ECC_ECC_SECP224R1_ENABLED
#define NRF_CRYPTO_BACKEND_MICRO_ECC_ECC_SECP224R1_ENABLED 0
#endif

// <q> NRF_CRYPTO_BACKEND_MICRO_ECC_ECC_SECP256R1_ENABLED  - Enable secp256r1 (NIST 256-bit) curve


// <i> Enable this setting if you need secp256r1 (NIST 256-bit) support using micro-ecc

#ifndef NRF_CRYPTO_BACKEND_MICRO_ECC_ECC_SECP256R1_ENABLED
#define NRF_CRYPTO_BACKEND_MICRO_ECC_ECC_SECP256R1_ENABLED 1
#endif

// <q> NRF_CRYPTO_BACKEND_MICRO_ECC_ECC_SECP256K1_ENABLED  - Enable secp256k1 (Koblitz 256-bit) curve


// <i> Enable this setting if you need secp256k1 (Koblitz 256-bit) support using micro-ecc

#ifndef NRF_CRYPTO_BACKEND_MICRO_ECC_ECC_SECP256K1_ENABLED
#define NRF_CRYPTO_BACKEND_MICRO_ECC_ECC_SECP256K1_ENABLED 0
#endif

// </e>

// <e> NRF_CRYPTO_BACKEND_NRF_HW_RNG_ENABLED - Enable the nRF HW RNG backend.

// <i> The nRF HW backend provide access to RNG peripheral in nRF5x devices.
//==========================================================
#ifndef NRF_CRYPTO_BACKEND_NRF_HW_RNG_ENABLED
#define NRF_CRYPTO_BACKEND_NRF_HW_RNG_ENABLED 0
#endif
// <q> NRF_CRYPTO_BACKEND_NRF_HW_RNG_MBEDTLS_CTR_DRBG_ENABLED  - Enable mbed TLS CTR-DRBG algorithm.


// <i> Enable mbed TLS CTR-DRBG standardized by NIST (NIST SP 800-90A Rev. 1). The nRF HW RNG is used as an entropy source for seeding.

#ifndef NRF_CRYPTO_BACKEND_NRF_HW_RNG_MBEDTLS_CTR_DRBG_ENABLED
#define NRF_CRYPTO_BACKEND_NRF_HW_RNG_MBEDTLS_CTR_DRBG_ENABLED 1
#endif

// </e>

// <e> NRF_CRYPTO_BACKEND_NRF_SW_ENABLED - Enable the legacy nRFx sw for crypto.

// <i> The nRF SW cryptography backend (only used in bootloader context).
//==========================================================
#ifndef NRF_CRYPTO_BACKEND_NRF_SW_ENABLED
#define NRF_CRYPTO_BACKEND_NRF_SW_ENABLED 1
#endif
// <q> NRF_CRYPTO_BACKEND_NRF_SW_HASH_SHA256_ENABLED  - nRF SW hash backend support for SHA-256


// <i> The nRF SW backend provide access to nRF SDK legacy hash implementation of SHA-256.

#ifndef NRF_CRYPTO_BACKEND_NRF_SW_HASH_SHA256_ENABLED
#define NRF_CRYPTO_BACKEND_NRF_SW_HASH_SHA256_ENABLED 1
#endif

// </e>

// <e> NRF_CRYPTO_BACKEND_OBERON_ENABLED - Enable the Oberon backend

// <i> The Oberon backend
//==========================================================
#ifndef NRF_CRYPTO_BACKEND_OBERON_ENABLED
#define NRF_CRYPTO_BACKEND_OBERON_ENABLED 0
#endif
// <q> NRF_CRYPTO_BACKEND_OBERON_CHACHA_POLY_ENABLED  - Enable the CHACHA-POLY mode using Oberon.


#ifndef NRF_CRYPTO_BACKEND_OBERON_CHACHA_POLY_ENABLED
#define NRF_CRYPTO_BACKEND_OBERON_CHACHA_POLY_ENABLED 0
#endif

// <q> NRF_CRYPTO_BACKEND_OBERON_ECC_SECP256R1_ENABLED  - Enable secp256r1 curve


// <i> Enable this setting if you need secp256r1 curve support using Oberon library

#ifndef NRF_CRYPTO_BACKEND_OBERON_ECC_SECP256R1_ENABLED
#define NRF_CRYPTO_BACKEND_OBERON_ECC_SECP256R1_ENABLED 1
#endif

// <q> NRF_CRYPTO_BACKEND_OBERON_ECC_CURVE25519_ENABLED  - Enable Curve25519 ECDH


// <i> Enable this setting if you need Curve25519 ECDH support using Oberon library

#ifndef NRF_CRYPTO_BACKEND_OBERON_ECC_CURVE25519_ENABLED
#define NRF_CRYPTO_BACKEND_OBERON_ECC_CURVE25519_ENABLED 0
#endif

// <q> NRF_CRYPTO_BACKEND_OBERON_ECC_ED25519_ENABLED  - Enable Ed25519 signature scheme


// <i> Enable this setting if you need Ed25519 support using Oberon library

#ifndef NRF_CRYPTO_BACKEND_OBERON_ECC_ED25519_ENABLED
#define NRF_CRYPTO_BACKEND_OBERON_ECC_ED25519_ENABLED 0
#endif

// <q> NRF_CRYPTO_BACKEND_OBERON_HASH_SHA256_ENABLED  - Oberon SHA-256 hash functionality


// <i> Oberon backend implementation for SHA-256.

#ifndef NRF_CRYPTO_BACKEND_OBERON_HASH_SHA256_ENABLED
#define NRF_CRYPTO_BACKEND_OBERON_HASH_SHA256_ENABLED 1
#endif

// <q> NRF_CRYPTO_BACKEND_OBERON_HASH_SHA512_ENABLED  - Oberon SHA-512 hash functionality


// <i> Oberon backend implementation for SHA-512.

#ifndef NRF_CRYPTO_BACKEND_OBERON_HASH_SHA512_ENABLED
#define NRF_CRYPTO_BACKEND_OBERON_HASH_SHA512_ENABLED 0
#endif

// <q> NRF_CRYPTO_BACKEND_OBERON_HMAC_SHA256_ENABLED  - Oberon HMAC using SHA-256


// <i> Oberon backend implementation for HMAC using SHA-256.

#ifndef NRF_CRYPTO_BACKEND_OBERON_HMAC_SHA256_ENABLED
#define NRF_CRYPTO_BACKEND_OBERON_HMAC_SHA256_ENABLED 0
#endif

// <q> NRF_CRYPTO_BACKEND_OBERON_HMAC_SHA512_ENABLED  - Oberon HMAC using SHA-512


// <i> Oberon backend implementation for HMAC using SHA-512.

#ifndef NRF_CRYPTO_BACKEND_OBERON_HMAC_SHA512_ENABLED
#define NRF_CRYPTO_BACKEND_OBERON_HMAC_SHA512_ENABLED 0
#endif

// </e>

// <q> NRF_CRYPTO_CURVE25519_BIG_ENDIAN_ENABLED  - Big-endian byte order in raw Curve25519 data


// <i> Enable big-endian byte order in Curve25519 API, if set to 1. Use little-endian, if set to 0.

#ifndef NRF_CRYPTO_CURVE25519_BIG_ENDIAN_ENABLED
#define NRF_CRYPTO_CURVE25519_BIG_ENDIAN_ENABLED 0
#endif

// </e>

// <h> nrf_crypto_rng - RNG Configuration

//==========================================================
// <q> NRF_CRYPTO_RNG_STATIC_MEMORY_BUFFERS_ENABLED  - Use static memory buffers for context and temporary init buffer.


// <i> Always recommended when using the nRF HW RNG as the context and temporary buffers are small. Consider disabling if using the CC310 RNG in a RAM constrained application. In this case, memory must be provided to nrf_crypto_rng_init, or it can be allocated internally provided that NRF_CRYPTO_ALLOCATOR does not allocate memory on the stack.

#ifndef NRF_CRYPTO_RNG_STATIC_MEMORY_BUFFERS_ENABLED
#define NRF_CRYPTO_RNG_STATIC_MEMORY_BUFFERS_ENABLED 1
#endif

// <q> NRF_CRYPTO_RNG_AUTO_INIT_ENABLED  - Initialize the RNG module automatically when nrf_crypto is initialized.


// <i> Automatic initialization is only supported with static or internally allocated context and temporary memory.

#ifndef NRF_CRYPTO_RNG_AUTO_INIT_ENABLED
#define NRF_CRYPTO_RNG_AUTO_INIT_ENABLED 1
#endif

// </h>
//==========================================================

// </h>
//==========================================================

// <h> nRF_DFU

//==========================================================
// <h> nrf_dfu - Device Firmware Upgrade

//==========================================================
// <h> DFU transport

//==========================================================
// <e> NRF_DFU_TRANSPORT_BLE - BLE transport settings
//==========================================================
#ifndef NRF_DFU_TRANSPORT_BLE
#define NRF_DFU_TRANSPORT_BLE 1
#endif
// <s> NRF_DFU_BLE_ADV_NAME - Default advertising name.
#ifndef NRF_DFU_BLE_ADV_NAME
#define NRF_DFU_BLE_ADV_NAME    "MW_DFU"
#endif

// <o> NRF_DFU_BLE_ADV_INTERVAL - Advertising interval (in units of 0.625 ms)
#ifndef NRF_DFU_BLE_ADV_INTERVAL
#define NRF_DFU_BLE_ADV_INTERVAL 40
#endif

// <h> BLE DFU security

//==========================================================
// <q> NRF_DFU_BLE_REQUIRES_BONDS  - Require bond with peer.


#ifndef NRF_DFU_BLE_REQUIRES_BONDS
#define NRF_DFU_BLE_REQUIRES_BONDS 0
#endif

// </h>
//==========================================================

// <h> BLE DFU connection

//==========================================================
// <o> NRF_DFU_BLE_MIN_CONN_INTERVAL - Minimum connection interval (units).
// <i> Minimum GAP connection interval, in 1.25 ms units.

#ifndef NRF_DFU_BLE_MIN_CONN_INTERVAL
#define NRF_DFU_BLE_MIN_CONN_INTERVAL 12
#endif

// <o> NRF_DFU_BLE_MAX_CONN_INTERVAL - Maximum connection interval (units).
// <i> Maximum GAP connection interval, in 1.25 ms units.

#ifndef NRF_DFU_BLE_MAX_CONN_INTERVAL
#define NRF_DFU_BLE_MAX_CONN_INTERVAL 12
#endif

// <o> NRF_DFU_BLE_CONN_SUP_TIMEOUT_MS - Supervision timeout (ms).
// <i> GAP connection supervision timeout, in milliseconds.

#ifndef NRF_DFU_BLE_CONN_SUP_TIMEOUT_MS
#define NRF_DFU_BLE_CONN_SUP_TIMEOUT_MS 6000
#endif

// </h>
//==========================================================

// <h> BLE DFU buffers

//==========================================================
// <e> NRF_DFU_BLE_BUFFERS_OVERRIDE

// <i> Check this option to override the default number of buffers.
//==========================================================
#ifndef NRF_DFU_BLE_BUFFERS_OVERRIDE
#define NRF_DFU_BLE_BUFFERS_OVERRIDE 0
#endif
// <o> NRF_DFU_BLE_BUFFERS - Number of buffers in the BLE transport.
// <i> Number of buffers to store incoming data while it is being written to flash.
// <i> Reduce this value to save RAM. If this value is too low, the DFU process will fail.

#ifndef NRF_DFU_BLE_BUFFERS
#define NRF_DFU_BLE_BUFFERS 8
#endif

// </e>

// </h>
//==========================================================

// </e>

// </h>
//==========================================================

// <h> DFU protocol

//==========================================================
// <q> NRF_DFU_PROTOCOL_FW_VERSION_MSG  - Firmware version message support.


// <i> Firmware version message support.
// <i> If disabled, firmware version requests will return NRF_DFU_RES_CODE_OP_CODE_NOT_SUPPORTED.

#ifndef NRF_DFU_PROTOCOL_FW_VERSION_MSG
#define NRF_DFU_PROTOCOL_FW_VERSION_MSG 1
#endif

// <q> NRF_DFU_PROTOCOL_VERSION_MSG  - Protocol version message support.


// <i> Protocol version message support.
// <i> If disabled, protocol version requests will return NRF_DFU_RES_CODE_OP_CODE_NOT_SUPPORTED.

#ifndef NRF_DFU_PROTOCOL_VERSION_MSG
#define NRF_DFU_PROTOCOL_VERSION_MSG 1
#endif

// </h>
//==========================================================

// <h> DFU security

//==========================================================
// <q> NRF_DFU_APP_DOWNGRADE_PREVENTION  - Check the firmware version and SoftDevice requirements of application (and SoftDevice) updates.


// <i> Whether to check the incoming version against the version of the existing app and/or
// <i> the incoming SoftDevice requirements against the existing SoftDevice.
// <i> This applies to application updates, and possibly to SoftDevice updates.
// <i> Disabling this causes the checks to always ignore the incoming firmware version and
// <i> to ignore the SoftDevice requirements if the first requirement is 0.
// <i> This does not apply the bootloader updates. If the bootloader depends on the SoftDevice
// <i> e.g. for BLE transport, this does not apply to SoftDevice updates.
// <i> See @ref lib_bootloader_dfu_validation for more information.
// <i> When signed updates are required, version checking should always be enabled.

#ifndef NRF_DFU_APP_DOWNGRADE_PREVENTION
#define NRF_DFU_APP_DOWNGRADE_PREVENTION 1
#endif

// <q> NRF_DFU_FORCE_DUAL_BANK_APP_UPDATES  - Accept only dual-bank application updates.


// <i> If not enabled then if there is not enough space to perform dual-bank update
// <i> application is deleted and single-bank update is performed. In case it is considered
// <i> security concern user can prefer to discard update request rather than overwrite
// <i> current application.

#ifndef NRF_DFU_FORCE_DUAL_BANK_APP_UPDATES
#define NRF_DFU_FORCE_DUAL_BANK_APP_UPDATES 0
#endif

// <o> NRF_DFU_HW_VERSION - Device hardware version.
// <i> This is used to determine if given update is targeting the device.
// <i> It is checked against the hw_version value in the init packet

#ifndef NRF_DFU_HW_VERSION
#define NRF_DFU_HW_VERSION 52
#endif

// <q> NRF_DFU_REQUIRE_SIGNED_APP_UPDATE  - Require a valid signature to update the application or SoftDevice.


#ifndef NRF_DFU_REQUIRE_SIGNED_APP_UPDATE
#define NRF_DFU_REQUIRE_SIGNED_APP_UPDATE 1
#endif

// <q> NRF_DFU_SINGLE_BANK_APP_UPDATES  - Place the application and the SoftDevice directly where they are supposed to be.


// <i> Note that this creates security concerns when signing and  version checks
// <i> are enabled. An attacker will be able to delete (but not replace)
// <i> the current app or SoftDevice without knowing the signature key.

#ifndef NRF_DFU_SINGLE_BANK_APP_UPDATES
#define NRF_DFU_SINGLE_BANK_APP_UPDATES 0
#endif

// </h>
//==========================================================

// <h> Misc DFU settings

//==========================================================
// <o> NRF_DFU_APP_DATA_AREA_SIZE - The size (in bytes) of the flash area reserved for application data.
// <i> This area is found at the end of the application area, next to the start of
// <i> the bootloader. This area will not be erased by the bootloader during a
// <i> firmware upgrade. The size must be a multiple of the flash page size.

#ifndef NRF_DFU_APP_DATA_AREA_SIZE
#define NRF_DFU_APP_DATA_AREA_SIZE 12288
#endif

// <q> NRF_DFU_SAVE_PROGRESS_IN_FLASH  - Save DFU progress in flash.


// <i> Save DFU progress to flash so that it can be resumed if interrupted, instead of being restarted.
// <i> Keep this setting disabled to maximize transfer speed and minimize flash wear.
// <i> The init packet is always saved in flash, regardless of this setting.

#ifndef NRF_DFU_SAVE_PROGRESS_IN_FLASH
#define NRF_DFU_SAVE_PROGRESS_IN_FLASH 0
#endif

// <q> NRF_DFU_SETTINGS_ALLOW_UPDATE_FROM_APP  - Whether to allow the app to receive firmware updates for the bootloader to activate.


// <i> Enable this to allow the app to instruct the bootloader to activate firmware.
// <i> The bootloader will perform only a cursory check on the firmware (CRC).

#ifndef NRF_DFU_SETTINGS_ALLOW_UPDATE_FROM_APP
#define NRF_DFU_SETTINGS_ALLOW_UPDATE_FROM_APP 0
#endif

// <q> NRF_DFU_SETTINGS_IN_APP  - Specifies that this code is in the app, not the bootloader, so some settings are off-limits.


// <i> Enable this to disable writing to areas of the settings that are protected
// <i> by the bootlader. If this is not enabled in the app, certain settings write
// <i> operations will cause HardFaults or will be ignored.

#ifndef NRF_DFU_SETTINGS_IN_APP
#define NRF_DFU_SETTINGS_IN_APP 0
#endif

// </h>
//==========================================================

// </h>
//==========================================================

// </h>
//==========================================================

// <h> nRF_Libraries

//==========================================================
// <e> APP_SCHEDULER_ENABLED - app_scheduler - Events scheduler
//==========================================================
#ifndef APP_SCHEDULER_ENABLED
#define APP_SCHEDULER_ENABLED 1
#endif
// <q> APP_SCHEDULER_WITH_PAUSE  - Enabling pause feature


#ifndef APP_SCHEDULER_WITH_PAUSE
#define APP_SCHEDULER_WITH_PAUSE 0
#endif

// <q> APP_SCHEDULER_WITH_PROFILER  - Enabling scheduler profiling


#ifndef APP_SCHEDULER_WITH_PROFILER
#define APP_SCHEDULER_WITH_PROFILER 0
#endif

// </e>

// <q> CRC32_ENABLED  - crc32 - CRC32 calculation routines


#ifndef CRC32_ENABLED
#define CRC32_ENABLED 1
#endif

// <e> MEM_MANAGER_ENABLED - mem_manager - Dynamic memory allocator
//==========================================================
#ifndef MEM_MANAGER_ENABLED
#define MEM_MANAGER_ENABLED 1
#endif
// <o> MEMORY_MANAGER_SMALL_BLOCK_COUNT - Size of each memory blocks identified as 'small' block.  <0-255>


#ifndef MEMORY_MANAGER_SMALL_BLOCK_COUNT
#define MEMORY_MANAGER_SMALL_BLOCK_COUNT 1
#endif

// <o> MEMORY_MANAGER_SMALL_BLOCK_SIZE -  Size of each memory blocks identified as 'small' block.
// <i>  Size of each memory blocks identified as 'small' block. Memory block are recommended to be word-sized.

#ifndef MEMORY_MANAGER_SMALL_BLOCK_SIZE
#define MEMORY_MANAGER_SMALL_BLOCK_SIZE 32
#endif

// <o> MEMORY_MANAGER_MEDIUM_BLOCK_COUNT - Size of each memory blocks identified as 'medium' block.  <0-255>


#ifndef MEMORY_MANAGER_MEDIUM_BLOCK_COUNT
#define MEMORY_MANAGER_MEDIUM_BLOCK_COUNT 0
#endif

// <o> MEMORY_MANAGER_MEDIUM_BLOCK_SIZE -  Size of each memory blocks identified as 'medium' block.
// <i>  Size of each memory blocks identified as 'medium' block. Memory block are recommended to be word-sized.

#ifndef MEMORY_MANAGER_MEDIUM_BLOCK_SIZE
#define MEMORY_MANAGER_MEDIUM_BLOCK_SIZE 256
#endif

// <o> MEMORY_MANAGER_LARGE_BLOCK_COUNT - Size of each memory blocks identified as 'large' block.  <0-255>


#ifndef MEMORY_MANAGER_LARGE_BLOCK_COUNT
#define MEMORY_MANAGER_LARGE_BLOCK_COUNT 0
#endif

// <o> MEMORY_MANAGER_LARGE_BLOCK_SIZE -  Size of each memory blocks identified as 'large' block.
// <i>  Size of each memory blocks identified as 'large' block. Memory block are recommended to be word-sized.

#ifndef MEMORY_MANAGER_LARGE_BLOCK_SIZE
#define MEMORY_MANAGER_LARGE_BLOCK_SIZE 256
#endif

// <o> MEMORY_MANAGER_XLARGE_BLOCK_COUNT - Size of each memory blocks identified as 'extra large' block.  <0-255>


#ifndef MEMORY_MANAGER_XLARGE_BLOCK_COUNT
#define MEMORY_MANAGER_XLARGE_BLOCK_COUNT 0
#endif

// <o> MEMORY_MANAGER_XLARGE_BLOCK_SIZE -  Size of each memory blocks identified as 'extra large' block.
// <i>  Size of each memory blocks identified as 'extra large' block. Memory block are recommended to be word-sized.

#ifndef MEMORY_MANAGER_XLARGE_BLOCK_SIZE
#define MEMORY_MANAGER_XLARGE_BLOCK_SIZE 1320
#endif

// <o> MEMORY_MANAGER_XXLARGE_BLOCK_COUNT - Size of each memory blocks identified as 'extra extra large' block.  <0-255>


#ifndef MEMORY_MANAGER_XXLARGE_BLOCK_COUNT
#define MEMORY_MANAGER_XXLARGE_BLOCK_COUNT 0
#endif

// <o> MEMORY_MANAGER_XXLARGE_BLOCK_SIZE -  Size of each memory blocks identified as 'extra extra large' block.
// <i>  Size of each memory blocks identified as 'extra extra large' block. Memory block are recommended to be word-sized.

#ifndef MEMORY_MANAGER_XXLARGE_BLOCK_SIZE
#define MEMORY_MANAGER_XXLARGE_BLOCK_SIZE 3444
#endif

// <o> MEMORY_MANAGER_XSMALL_BLOCK_COUNT - Size of each memory blocks identified as 'extra small' block.  <0-255>


#ifndef MEMORY_MANAGER_XSMALL_BLOCK_COUNT
#define MEMORY_MANAGER_XSMALL_BLOCK_COUNT 0
#endif

// <o> MEMORY_MANAGER_XSMALL_BLOCK_SIZE -  Size of each memory blocks identified as 'extra small' block.
// <i>  Size of each memory blocks identified as 'extra large' block. Memory block are recommended to be word-sized.

#ifndef MEMORY_MANAGER_XSMALL_BLOCK_SIZE
#define MEMORY_MANAGER_XSMALL_BLOCK_SIZE 64
#endif

// <o> MEMORY_MANAGER_XXSMALL_BLOCK_COUNT - Size of each memory blocks identified as 'extra extra small' block.  <0-255>


#ifndef MEMORY_MANAGER_XXSMALL_BLOCK_COUNT
#define MEMORY_MANAGER_XXSMALL_BLOCK_COUNT 0
#endif

// <o> MEMORY_MANAGER_XXSMALL_BLOCK_SIZE -  Size of each memory blocks identified as 'extra extra small' block.
// <i>  Size of each memory blocks identified as 'extra extra small' block. Memory block are recommended to be word-sized.

#ifndef MEMORY_MANAGER_XXSMALL_BLOCK_SIZE
#define MEMORY_MANAGER_XXSMALL_BLOCK_SIZE 32
#endif

// <e> MEM_MANAGER_CONFIG_LOG_ENABLED - Enables logging in the module.
//==========================================================
#ifndef MEM_MANAGER_CONFIG_LOG_ENABLED
#define MEM_MANAGER_CONFIG_LOG_ENABLED 0
#endif
// <o> MEM_MANAGER_CONFIG_LOG_LEVEL  - Default Severity level

// <0=> Off
// <1=> Error
// <2=> Warning
// <3=> Info
// <4=> Debug

#ifndef MEM_MANAGER_CONFIG_LOG_LEVEL
#define MEM_MANAGER_CONFIG_LOG_LEVEL 3
#endif

// <o> MEM_MANAGER_CONFIG_INFO_COLOR  - ANSI escape code prefix.

// <0=> Default
// <1=> Black
// <2=> Red
// <3=> Green
// <4=> Yellow
// <5=> Blue
// <6=> Magenta
// <7=> Cyan
// <8=> White

#ifndef MEM_MANAGER_CONFIG_INFO_COLOR
#define MEM_MANAGER_CONFIG_INFO_COLOR 0
#endif

// <o> MEM_MANAGER_CONFIG_DEBUG_COLOR  - ANSI escape code prefix.

// <0=> Default
// <1=> Black
// <2=> Red
// <3=> Green
// <4=> Yellow
// <5=> Blue
// <6=> Magenta
// <7=> Cyan
// <8=> White

#ifndef MEM_MANAGER_CONFIG_DEBUG_COLOR
#define MEM_MANAGER_CONFIG_DEBUG_COLOR 0
#endif

// </e>

// <q> MEM_MANAGER_DISABLE_API_PARAM_CHECK  - Disable API parameter checks in the module.


#ifndef MEM_MANAGER_DISABLE_API_PARAM_CHECK
#define MEM_MANAGER_DISABLE_API_PARAM_CHECK 0
#endif

// </e>

// <e> NRF_BALLOC_ENABLED - nrf_balloc - Block allocator module
//==========================================================
#ifndef NRF_BALLOC_ENABLED
#define NRF_BALLOC_ENABLED 1
#endif
// <e> NRF_BALLOC_CONFIG_DEBUG_ENABLED - Enables debug mode in the module.
//==========================================================
#ifndef NRF_BALLOC_CONFIG_DEBUG_ENABLED
#define NRF_BALLOC_CONFIG_DEBUG_ENABLED 0
#endif
// <o> NRF_BALLOC_CONFIG_HEAD_GUARD_WORDS - Number of words used as head guard.  <0-255>


#ifndef NRF_BALLOC_CONFIG_HEAD_GUARD_WORDS
#define NRF_BALLOC_CONFIG_HEAD_GUARD_WORDS 1
#endif

// <o> NRF_BALLOC_CONFIG_TAIL_GUARD_WORDS - Number of words used as tail guard.  <0-255>


#ifndef NRF_BALLOC_CONFIG_TAIL_GUARD_WORDS
#define NRF_BALLOC_CONFIG_TAIL_GUARD_WORDS 1
#endif

// <q> NRF_BALLOC_CONFIG_BASIC_CHECKS_ENABLED  - Enables basic checks in this module.
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
